Dylan-Hackett/vuulgaris-v1/docs/lpg-bergman.md

# Stereo low pass gate — Eddy Bergman's Buchla 292

Transcribed 2026-09-04 from **"RESONANT LOPASS GATE (BASED ON BUCHLA 292)",
schematic redrawn by Eddy Bergman**, 4500 x 4500 JPEG from
[eddybergman.com part 35](https://www.eddybergman.com/2020/10/synthesizer-build-part-35-resonant.html).
Raster, not vector — so unlike the BBD there is a hard resolution floor, but at
4500px the values and junctions read cleanly at 60% zoom.

## Licensing — read before this goes anywhere near a product

The drawing carries **"not for commercial use!"** in its own bottom-right corner.
`design-state.md:248` records the design as "free, he invites builds", which is
true of DIY, and §6 already notes that redrawing it is "the right move IP-wise".
Those are not the same permission. This repo also contains plans for JLC
assembly and EU sales. If this is ever sold, work from the **modularsynthesis.com
Buchla 292 source Bergman says he redrew from**, not from his drawing.

## What it is

Two vactrols per channel whose LDRs sit in the audio path, driven by a common
LED string. A 3-position mode switch reconfigures the same LDR pair as a VCA, a
2-pole resonant low pass, or both at once. `U1` is a TL084 (four sections),
`U2` a TL074 doing the CV mixing.

## Audio path, one channel

```
AUDIO IN ─┬─ R9 100K ─ GND        <- BEFORE the cap, loads the source
          └─ C6 1uF ─┬─ R10 100K ─ GND    <- AFTER it, biases the input
                     └─ U1-A pin 3 (+)
    U1-A pin 2 (−) ─┬─ R11 15K ─ pin 1 (out)
                    └─ R12 15K ─ [S1/S2] ─ GND     gain 2 with the contact made,
                                                    1 with it open
    pin 1 ─ LDR1 ─┬─ LDR2 ─┬─ R16 10K ─ [S3/S4] ─ GND
                  │        └─ U1-C pin 10 (+) ─┬─ C9 1nF ─ GND
                  │                            └─ R13 4M7 ─ GND
                  ├─ C7 220pF ─ GND
                  └─ C8 4.7nF ─ [S5/S6] ─ U1-D pin 14 (out)

    U1-C pin 9 (−) ─ R14 10K ─ pin 8 (out)         unity buffer
    pin 8 ─ R15 1K ─ AUDIO OUT
    pin 8 ─ U1-D pin 12 (+)
    U1-D pin 13 (−) ─ C10 22pF / RESONANCE 100K / R18 100K
```

**`U1-C` is the output buffer and `U1-D` is the resonance amplifier** — not the
other way round, which is the easy misreading. The LDR chain feeds `U1-C`'s
**non-inverting** input directly; `C9` 1nF and `R13` 4M7 sit on that node. `U1-C`
buffers to the output *and* drives `U1-D`, whose output returns through `C8` into
the **junction between the two LDRs** — the mid-node of the two-pole filter,
which is where resonance feedback belongs. RESONANCE sets how much comes back.

### Careful: the drawing uses "S1" for two different things

Bergman labels the **mode switch's first lug** `S1` (the red dot by `R12`) *and*
the **DEEP toggle** `S1 DEEP on/off`. They are unrelated parts. Everywhere below,
`S1`-`S6` mean mode-switch lugs only; the DEEP toggle is not fitted (see LED
drive).

### The mode switch is the whole trick

The table on the drawing is captioned **"Bottom view of toggle switch"** — it is a
**lug map, not a list of closed contacts**, and misreading it that way inverts the
whole circuit. In a 3PDT toggle the middle row of lugs is the three commons, so
**S2, S4 and S5 are commons**, and on an ON-OFF-ON the centre lever position
connects them to nothing.

| lever | contacts made | circuit |
|---|---|---|
| **VCA** | S2-S1, S4-S3 | `R12` grounded (gain 2), `R16` grounded. LDRs plus `R16` are a defined divider, response stays flat. `C8` open |
| **BOTH** (middle = OFF) | **none** | `R12`, `R16` and `C8` all open. The LDRs feed only `C7`, so the series photoresistance drops level and corner frequency **together** |
| **VCF** | S5-S6 | `C8` into the LDR1/LDR2 junction — 2-pole resonant lowpass |

**BOTH is not a combination of the other two.** It is the bare behaviour of a
photoresistor in series with a capacitor, with the switch removed from the
circuit entirely — which is the actual Buchla lowpass-gate character. VCA and VCF
are each a *modification* of it: `R16` pins the response flat, `C8` plus
resonance makes it a filter.

**Consequence for the switch part.** Poles 1 and 2 always act together, so there
are only **two** control signals — "ground `R12` and `R16`" and "connect `C8`" —
not three, and the middle position switches nothing. Stereo therefore needs
**four switched connections**, which is a quad analog switch, not the 6P3T panel
toggle this otherwise implies.

## LED drive — verified 2026-09-04 at 1.7x

`U1-B` is an **inverting** amp: pin 5 (+) runs left and straight down to `R8` 10K
to ground, **crossing `R5`'s line with no junction dot** — checked at high zoom,
and reading that crossing as a connection would turn the stage into a follower.

Its inverting input is the summing node, and OFFSET and CV arrive there
differently:

```
OFFSET pot wiper ─ R3 150K ─┬──────────── U1-B pin 6 (−)      [same node]
                            ├─ R5 100K ──────────┐
                            └─ C5 2nF ─ R4 470K ─┴─ CV in (U2-C output)
```

`C5` and `R4` are in **series with each other** and that pair is in **parallel
with `R5`** — both between the summing node and the CV node. At DC `C5` blocks,
so the CV sees 100K. Above about 170Hz it shorts and the branch becomes `R4`
470K in parallel with `R5`, i.e. 82.5K, giving the CV path roughly **1.2x more
gain at high frequency**. That is deliberate: it sharpens envelope transients to
compensate for how slow a vactrol is.

### Two feedback paths, not one

```
pin 6 ─┬─ Tp2 500K trim ──────────────────────────── pin 7 (out)   [S1 removed]
       └─ Tp1 20K trim ─ R7 33K ─┬─ LED anode node
                                 ├─ R17 100K ─ GND
                                 ├─ D1 3.9V zener, ANODE here, cathode to GND
                                 └─ VT_a LED anode
                                      VT_a cathode ─ VT_b anode
                                        VT_b cathode ─ R6 470R ─ pin 7 (out)
```

**The LED string never touches ground.** Its far end returns to the op-amp
output through `R6`; ground reaches the string only through `D1` and `R17`.

`U1-B` swings **negative**, because OFFSET sits on the positive rail and feeds
an inverting stage. So the anode node sits at **−3.9V**, where `D1` is in
reverse breakdown, and **`D1` is what supplies the LED current** — from ground,
through the string, into pin 7, which sinks it. `R6` and the output voltage set
how much. `Tp1` sets the feedback depth from that node; `Tp2` adds a second
feedback path taken straight from the output, changing overall gain.

> **Corrected 2026-09-16.** Every earlier version of this section, and the
> schematic built from it, had this backwards: `R6` on the anode side, both LED
> cathodes to ground, and `D1` reversed. That inverts the drive. With our
> op-amp swinging negative, the flipped `D1` pins the node at −0.7V and the LEDs
> never light; and where the real circuit has `D1` *supplying* LED current, the
> flipped one *shunts* it away above 3.9V. The 2026-09-11 "node by node, both
> channels, clean" check compared the netlist against this document rather than
> against Bergman's drawing, so both were wrong together — the same failure as
> U8. Fixed on the board 2026-09-16: `D301`/`D401` turned around,
> `VT302.2`/`VT402.2` moved off GND onto `LPG_LEDK_L`/`_R`, and `R306`/`R406`
> moved to sit between the LED cathodes and the op-amp output.

**Neither `S1` "DEEP" nor `Tp2` is fitted — decided 2026-09-04.** Bergman
describes DEEP as making the sound "deeper with less high tones… the effect of
turning the Offset knob counterclockwise, amount set by `Tp2`". Mechanically it
adds a second feedback path from pin 7 straight to the summing node, bypassing
the LEDs, so part of the feedback stops depending on the LED node and the LED
node has to move less to balance. Less light, gate sits more closed — an
operating-point shift, not a filter change.

With the switch permanently open that path never exists, so **`Tp2` has nothing
to do and is not fitted either.** `RT302`/`RT402` removed. `Tp1` (`RT301`/`RT401`)
stays: it is in the main loop and is still the LED-drive depth trim.

**LED reverse-voltage protection, added 2026-10.** Without DEEP's path, nothing
holds pin 7 in when the summing node goes negative (an inverted CV with CUTOFF
low), so `U1-B` saturates positive, about +10V, while the LED node sits near 0V
through `R317`. The two LEDs then take about 10V in reverse against the VTL5C3's
3.0V absolute maximum ("LED Reverse Breakdown Voltage", Xvive p1). Bergman's
circuit does the same with DEEP off. Fix:

- `D302`/`D402`, a 1N4148W in series between the LED string and `R306`/`R406`:
  anode on `LPG_LEDK_L`/`_R`, cathode on the new `LPG_LEDD_L`/`_R`, which is
  `R306.2`/`R406.2`. It carries the LED current forward and blocks the reverse
  voltage (VR 75V; 25nA max at 20V, `datasheets/1N4148W.pdf`).
- `R334`/`R434`, 2.2M across the LED pair (`LPG_LED` to `LPG_LEDK`). Two parts in
  series in reverse share the voltage by their leakage, so on its own the diode
  could leave the LEDs most of it. The resistor holds the LEDs at the diode's
  leakage times 2.2M, about 55mV at 25nA. Forward it takes about 1.4uA at 3V,
  negligible against milliamps of LED drive.

Cost: one diode drop off the ceiling of the LED drive, about 1.5mA off the 9.1mA
worst-case maximum (recheck section 06). Below the ceiling nothing changes: the
diode is inside `U1-B`'s loop, which regulates the LED anode node, so pin 7 just
sits a diode drop lower for the same LED current. `RT301`/`RT401` cannot give
the 1.5mA back; they set feedback depth, not the ceiling, which is
(Vsat - Vz - 2Vf - Vdiode) / `R306`. `R306`/`R406` stay at Bergman's 470R, so
every state is at or below his circuit's LED current. If the gate does not open
far enough on the bench, 390R there restores the ceiling (worst case 9.2mA).

## CV section — `U2` TL074

`CV1 IN` through a **Level 100K** pot, its wiper into `R28` 100K; `CV2 IN`
into `R23` 100K at `U2-A` (`R20` 100K feedback) and across the **Level + Invert
100K** pot, whose wiper feeds `R27` 100K. `R27` and `R28` both land on `U2-D`
pin 13. (Corrected 2026-09-23 — this used to say CV1 fed both, and the drop
below named `R27` as CV1's. On the drawing `R27` is CV2's and `R28` is CV1's.)
`U2-D` (12/13/14, `R30` 100K feedback) sums, `R31` 100K feeds `U2-C` (10/9/8,
`R33` 100K feedback), whose output runs back to the `R4`/`R5` summing node in the
LED driver. **`U2-B` is unused.**

## Adaptation — decided 2026-09-04

**Rails: ±12V, unchanged.** Bergman runs ±15V. Accepted as-is; the LED drive
range, the `D1` 3.9V clamp point and the `R6` 470R current all shift slightly and
the trimmers (`Tp1` depth, `Tp2` gain) absorb it. Set them on the bench.

**Three panel pots, dual-gang, one knob per stereo pair:**

| | Bergman | here |
|---|---|---|
| `RV1` **CUTOFF** | OFFSET 100K | sets the standing LED drive — how open the gate rests |
| `RV2` **RESONANCE** | RESONANCE 100K | unchanged |
| `RV3` **CV AMOUNT** | CV2 "Level + Invert" 100K | bipolar attenuverter on `LPG_ENV` |

This settles the `values.json` vs `pin-allocation.md:408-410` disagreement in
favour of `values.json`. **`pin-allocation.md` is now stale** and should be
updated to match.

**CV1 is dropped entirely** — its jack, its Level pot, and `R28`. The resistor
kept, `R328`/`R428`, is electrically Bergman's **`R27`**: CV2's attenuverter
wiper into `U2-D` pin 13. Only the designator is off by one. `LPG_ENV` from
the Daisy's CV_OUT_1 is the only control voltage.

### Dropping CV1 frees a whole op-amp package

With `R28` gone, `U2-D` has a single input, so `U2-D` + `U2-C` are two cascaded
unity inverters — a buffer. Per channel `U2` needs only **`U2-A`** (the
attenuverter's inverter) and **one summing/buffer stage**, so:

- 2 sections per channel, 4 for stereo
- **one TL074 covers both channels** instead of two
- `U2-B` was already marked "not used" on the drawing

### Mode switch

Mechanically a 3PDT ON-OFF-ON, and `SW1` here is a DPDT which cannot do it. Per
the switch reading above the circuit needs only **two control signals** and
**four switched connections** for stereo, so a quad analog switch would cover it
from one plain panel toggle — `DG419DY-T1-E3` is in `lib/vuulgaris.kicad_sym`
and commit 6724750 took that route once.

**Superseded 2026-09-11: VCA was dropped, so this is moot.** Two modes need two
switched connections, one per channel, and the DPDT does that directly. See
*VCA mode is deliberately not implemented* above.

### Vactrols — still open

Four needed, matched in on-resistance and decay across L and R. Excelitas
discontinued the line; the Xvive reissue reportedly has a brighter LED and longer
release. `design-state` §6 also carries an **unverified RoHS/cadmium** question.
No symbol or footprint in `lib/` yet.

## Checked against the drawing — 2026-09-11, both channels

> **Two rows of this table were wrong and shipped into the board: the LED drive
> and the input stage.** Both were caught by eye, 2026-09-16, by reading the
> drawing at full resolution.
>
> **Re-read in full 2026-09-23**, the 6000px image against `netmap.json` itself
> rather than against this document, cropped to full resolution wherever the
> overview was ambiguous: the pin 5/`R8` crossing (a gap, no junction), `D1`
> (anode on the LED node), pin 7's vertical (stops at the DEEP switch, never
> reaches the LED anode), the `R3`/`C5`/`R4`/`R5` node pair, the input stage,
> and the C8 → VCF → `U1-D` out return. **Every row below matches the board.**
> The one error found was a name: `R27`/`R28`, above.

`datasheets/` now holds Bergman's schematic image. `netmap.json` was diffed
against it node by node, L and R. **The two channels are structurally identical**
— every node below has the same membership on both sides, so nothing is a
one-channel typo.

Matching, and including the three things this drawing is easy to get wrong:

| node | agrees |
|---|---|
| ~~input~~ | **WRONG — `R9` sits BEFORE `C6`, `R10` after it. This row put both after the cap and the board was built that way, giving 50k of bias instead of 100k and nothing loading the source. Fixed 2026-09-16: `R310`/`R410` moved to the pre-cap node, so on our board `R310` = Bergman's `R9` and `R309` = `R10`.** |
| `U1-A` | `R11` 15K feedback |
| vactrols | LEDs in series off `R6`; LDRs in series in the audio path |
| LDR mid-node | `C7` 220pF to GND |
| **`C8` 4.7nF** | mid-node → switch → **`U1-D` output**, not to ground — the resonance injection |
| LDR2 out | `C9` 1nF and `R13` 4M7 to GND, into `U1-C` pin 10 **(+)** |
| `U1-C` | `R14` unity buffer, `R15` to output, and it drives `U1-D` pin 12 |
| `U1-D` | `C10` 22pF, RESONANCE, `R18` |
| ~~**LED drive**~~ | **WRONG — see the correction in "Two feedback paths". The string's cathode end returns through `R6` to pin 7 and `D1`'s anode is on the node. This row claimed otherwise and the board was built from it. Fixed 2026-09-16.** |
| **offset/CV sum** | `R5` 100K in parallel with the `C5`+`R4` *series* pair |
| CV chain | `U2-A` inverter, `RV3` attenuverter, `U2-D`→`U2-C` cascade |
| `U2-B` | unused, pin 5 to GND, pins 6/7 tied — as drawn |

Zero dangling nets anywhere in the block.

Deviations that are deliberate and recorded above: CV1 and `R28` dropped, `Tp2`
and the DEEP switch not fitted, ±12V rails instead of ±15V, the LED
reverse-voltage diode and its 2.2M (2026-10), and, since
2026-09-25, the **input mix** below.

### The input is a mix of the Daisy and EXT — added 2026-09-25, ADR 0011

The LPG input used to be the Daisy's output alone, into `C306`/`C406` (Bergman's
`C6`). It is now a passive two-resistor mix into that same cap:

```
AUDIO_OUT ──────┬── R301 10k ──┬── C306 1u ── U301A (+)     U301A (−) ─┬─ R311 15k ─ out
          R310 100k (R9)       │                                       └─ R312 15k ─ GND
EXT_AMP_OUT ──── R302 10k ─────┘                   (L; R channel is the 4xx set)
```

`R312`/`R412` is **Bergman's own `R12`, fitted permanently to ground** instead of
switched in for VCA mode. With it, `U1-A` runs at gain 2, which takes back the 6dB
the passive mix costs: each source reaches the LDRs at 0.95x its old level. It does
**not** implement VCA mode — that needs `R16` as well, which is still absent. Why
the mix exists, and what it costs, is in ADR 0011.

### VCA mode is deliberately not implemented — decided, do not re-raise

**This instrument ships BOTH and VCF only.** Confirmed 2026-09-11. `R16` is on
Bergman's drawing and on neither channel here, and that is the intended design,
not an omission. (`R12` was omitted too until 2026-09-25; it is now fitted
permanently for the input mix above, which is not VCA mode.)

- `R12` 15K, `U1-A` pin 2 → [S1/S2] → GND. **Now fitted as `R312`/`R412`,
  straight to ground** — `U1-A` at gain 2 on a halved input, net unity. In
  Bergman's circuit it gives gain 2 only in VCA.
- `R16` 10K, LDR2 output → [S3/S4] → GND. Omitted, so nothing pins the response
  flat — which is the whole point of VCA mode.

`SW1` compounds it. It is a DPDT using pins 1/2 and 4/5 only, so each pole is
ON-OFF rather than ON-ON, and the one thing it switches is `C8`:

| `SW1` | result | Bergman equivalent |
|---|---|---|
| closed | `C8` → `U1-D` out | **VCF** — resonant 2-pole |
| open | `C8` floating | **BOTH** — bare LDR + `C7` |

That is exactly the wanted behaviour. **BOTH is the actual Buchla lowpass-gate
character** — series photoresistance dropping level and corner frequency
together — and VCF is the resonant variant. VCA, the mode that pins the response
flat and turns the thing into a plain amplifier, is the one worth losing.

Dropping it also simplifies the hardware rather than compromising it. The
three-mode circuit needs four switched connections for stereo, which is why
*Mode switch* below reached for a `DG419DY-T1-E3` quad analog switch. Two modes
need **two** connections — one per channel — so a plain DPDT panel toggle is not
a compromise here, it is the correct part. `SW1` is already wired that way,
using pins 1/2 and 4/5 so each pole is ON-OFF.

**The DG419 proposal is therefore moot and should not be implemented.** Anyone
restoring VCA would need the quad analog switch *and* four resistors
(`R312`/`R412`, `R316`/`R416`), and that is not on the roadmap.

## Interface this has to present

| net | direction | currently |
|---|---|---|
| `AUDIO_OUT_L` / `_R` | Daisy → LPG in | via `R301`/`R401` into the input mix |
| `EXT_AMP_OUT_L` / `_R` | EXT preamp → LPG in | via `R302`/`R402` into the input mix (ADR 0011) |
| `BBD_IN_L` / `_R` | LPG out → delay | only on `R106`/`R107`, `R206`/`R207` |
| `LPG_ENV` | Daisy CV_OUT_1 → LED drive | only on `U1.C10` |
| `RV1` `RV2` `RV3` | panel, dual-gang | **placed, zero pins wired** |
| `SW1` `SW2` | panel | **placed, zero pins wired** |

## Status — in netmap and VERIFIED 2026-09-04

**748/748 connections verified, 0 unintended, 189 nets, `netcheck` exits 0.**
netmap went 169 refs / 524 connections -> **245 / 748**.

**Built exactly as the drawing shows, per channel, with CV1 removed and nothing
else reasoned away.** 14 op-amp sections, four packages:

| | |
|---|---|
| `U301` / `U401` | Bergman `U1`. A input buffer, B LED driver, C output buffer, D resonance |
| `U302` / `U402` | Bergman `U2`. A attenuverter inverter, D summer, C output inverter, **B unused with pin 5 to GND and 6 tied to 7, as drawn** |
| `VT301/302`, `VT401/402` | four VTL5C3 |
| `RT301` / `RT401` | `Tp1` 20K LED-drive depth trim, one per channel. `Tp2` not fitted |

`RV1` CUTOFF, `RV2` RESONANCE, `RV3` CV AMOUNT and `SW1` had **zero pins wired**
before this and are now connected. `SW1` pole A switches `C308`, pole B `C408` —
open is BOTH, closed is VCF.

**Removed, all by explicit decision and not by inference:** the CV1 jack, its
Level pot and `R28`; the DEEP switch and `Tp2` with it; and
`R16`, because only BOTH and VCF modes are wanted so the VCA contact is
never made. (`R12` was on this list until 2026-09-25; it is now fitted as the input
mix's gain makeup.)

### Still to do

- **F8** to pull the footprints onto the board, then place.
- The **3V9 zener** is a generic `Device:D_Zener` on a SOD-123 land — pick a real
  part before ordering.
- **Vactrol pair-to-pair spacing** in `VACTROL-TH_VTL5C3` is 12.7mm, a layout
  choice not a package dimension; the 5.08mm within each pair is from the
  datasheet and is fixed.
- **Match the four vactrols** on on-resistance and decay, L against R.
- ~~**Two knobs turn the unconventional way**~~ — **flipped 2026-09-23.** Found
  once Alpha's drawing confirmed terminal 1 is CCW: `RV1` CUTOFF had `POS12V`
  on 1/4, so clockwise *closed* the gate, and `RV3` CV AMOUNT had `LPG_ENV` on
  1/4, so clockwise was the *inverted* envelope. Bergman's drawing does not say
  which lug is CW, so neither was a departure from the source — just a choice
  nobody made. Now `RV1` is GND 1/4, `POS12V` 3/6 (**clockwise opens**) and
  `RV3` is `LPG_ENVN` 1/4, `LPG_ENV` 3/6 (**clockwise is the normal envelope,
  noon is zero**). `RV2` RESONANCE was already conventional (CW = more).
- With `R16` unfitted the LDRs work into `R13` 4M7, so at full dark the gate
  reaches about **-14dB**, not silence — the "vactrol bleed" of `design-state` §6.
