Dylan-Hackett/vuulgaris-v1/docs/pin-allocation.md

# Pin allocation

**Status: CURRENT as of 2026-08-09.** Rewritten after a cascade of changes freed six pins
and added five jacks. Safe to lay out against.

## The IO plan

**Changed 2026-08-09: the ten Daisy-facing knobs are ENCODERS, not pots.**

- **10 rotary encoders** on **2x MCP23017 I2C expanders**, both on the MAIN PCB
  beside the encoders themselves. 20 lines into the expanders, **2 wires out**.
- **3 knobs stay ANALOG POTS wired straight to the Bergman LPG board**: offset
  (dual-gang), CV amount L, CV amount R. Zero pins, zero conversion, and the
  Daisy never sees them. **Deliberate: no DAC.**
- **The MSP430 link is UART on A2/A3**, point-to-point across the cable.
  **NOT on the I2C bus.** See "why the touch link is UART" below.
- **Four jacks** (J2-J5), **corrected 2026-09-06** -- the list below used to name five
  functions for four connectors, and two of its sources have since gone internal:

  | jack | source | note |
  |---|---|---|
  | J2 CV OUT | `LPG_ENV` via `R503` 1k | **shares the LPG envelope.** Not an independent DAC -- both CV outs are spoken for |
  | J3 GATE OUT | `GATE_OUT_1` (B5) via `R504` 1k | |
  | J4 CV IN | `CV_8` (C9) | conditioned on-module |
  | J5 GATE IN / clock | `GATE_IN_1` (B10) | |

  `CV_OUT_2` (C1) is `TIME_CV` and `GATE_OUT_2` (B6) is the BBD inhibit, so neither
  reaches the panel. `CV_1`-`CV_7`, `GATE_IN_2` and `A9` are still free if a fifth jack
  is ever wanted.
- **Main encoder on U4 (GPB0-2), not the Daisy.** A9 is free (shift was dropped).
- **A8 reserved**, see below. **1-bit SD.** No panel USB.

### MSP430 reset on U4 GPB3 — added 2026-09-08

`U4.4` (GPB3) drives `MSP_RST` across `J12.3`. **This is not BSL.** Blank detection
means the Daisy never needs the entry sequence; this is a recovery reset for a
touch chip that has hung, and the way to re-arm the BSL after SLAU550 §3.4's
ten-second time-out without power-cycling the module.

**On an expander GPIO, not a Daisy pin**, for three reasons. Every Daisy candidate
is gone — `B5` is the gate out jack, `B6` the BBD inhibit, `A9` the OLED reset,
`A8` reserved. U4 had GPIO to spare (it is full now, see "GPA7 and GPB7" below). And the expander runs on `P3V3_DAISY` against an
MSP430 absolute max of 3.6V, so it is a **direct wire with no divider** — which
is precisely what [Q13](notes/open-questions.md) called a day lost with a logic
analyser. Being on I2C rather than the UART also means it still works when the
touch chip is too wedged to answer on the serial link.

> **This makes a faceplate part load-bearing.** MCP23017 GPIO power up as
> **inputs (high-Z)**, so `MSP_RST` floats until firmware configures GPB3. The
> pullup and capacitor TI specifies on RST/NMI must be on the faceplate. It was
> good practice before; it is now required.

`MSP_TEST` stays undriven on `J12.1`. **No external pulldown** (corrected 2026-09-28; this
said it "still wants a pulldown at the chip end"): SLASEO5D Table 7-4 says an unused TEST is
left "Open. This pin always has an internal pulldown enabled", and Figure 10-4, TI's
Spy-Bi-Wire connection, puts nothing on it.

(J12 pin numbers changed 2026-09-25, when `J12` moved to the back of the main board facing
down — see `hardware/faceplate/README.md` §5 for the full pin map.)

### Four channel buttons — added 2026-08-16

**Four momentary buttons on U4's spare GPIO**, one per channel, sitting in the left
margin beside the pads. They cost **no Daisy pins**: U3 is full at 16 GPIO for eight
encoders, but U4 only used 4 of 16 for ENC9/ENC10, so the buttons take `GPA4`-`GPA7`
and eight of its GPIO are still free after them.

| Button | Net | U4 pin |
|---|---|---|
| SW4 | `BTN1` | 25 (GPA4) |
| SW5 | `BTN2` | 26 (GPA5) |
| SW6 | `BTN3` | 27 (GPA6) |
| SW7 | `BTN4` | 7 (GPB6), was 28 (GPA7) until 2026-10 |

Wired **button to ground with the MCP23017's internal pull-ups enabled** — the same
arrangement as the encoders, so no external resistors. Polled with everything else at
500Hz, i.e. 2ms, which is irrelevant for a button.

**Placement, revised 2026-08-17:** the controls sit in the left margin centred on panel
**x 33.571** — the main encoder at y 76.525, then the four keys as a **2x2 Cherry MX
cluster** on 19.05mm pitch at x 24.046 / 43.096, y 100.725 / 119.775. The pad block moved
**20mm right** to open that margin, so the pads now run x 61.143-277.143. The encoder
used to sit in the RIGHT margin; it moved with the keys so the UI reads as one group.

**There is no shift button.** It was dropped 2026-08-16 — the four keys are general UI
keys, not per-channel modifiers, which is why they read better as a cluster than a
column. A9 came back with it.

Everything else on the panel is unchanged — the ten parameter encoders, three pots, two
DPDT switches and the OLED keep their coordinates, because the upper region is centred
independently of the pad block.

**This displaced the MSP430 power cluster**, which was in that left margin. It moved to
pcb (40-62, 98-105) — still nowhere near the OLED rail, which is the only thing §5.5
actually requires of it.

**`placement-panel-facing.txt` is now genuinely generated:**
`python3 mockups/generate-faceplate.py --placement > hardware/placement-panel-facing.txt`.
It previously claimed to be generated while being hand-maintained, which let the panel
artwork and the PCB placement drift apart with nothing to catch it.

**Net names are placeholders.** `BTN1`-`BTN4` should be renamed once the function is
decided (mute? solo? channel select? record-arm?).

### Two links, deliberately separate

| Link | Daisy pins | Devices | Crosses the cable? |
|---|---|---|---|
| **UART4** | **A2** (RX), **A3** (TX) | MSP430FR2675 | **yes**, point-to-point |
| **I2C1** | B7 (SCL), B8 (SDA) | MCP23017 x2 @ 0x20, 0x21 | **no**, main PCB only |

### Poll rates, and the arithmetic behind them

Quadrature edges per second is `rev/sec x PPR x 4`. For a 24-PPR encoder that is
**96 edges per revolution**, so:

| turn | rev/sec | edges/sec | at 500Hz | at 2kHz |
|---|---|---|---|---|
| deliberate parameter twist | ~1 | ~96 | 5 samples/edge | 21 |
| **fast menu flick** | 3-5 | **288-480** | **1-2 samples/edge** | 4-7 |

**ENC1-ENC10 stay at 500Hz** — about 24% of a 400kHz bus for both expanders. Parameter
knobs are turned deliberately and never flicked through a list.

**U4's Port B is polled at 2kHz** because ENC0 lives there and ENC0 is the one encoder
that does get spun hard. One GPIOB read is about 100us, so that is roughly 20% more bus.

### GPA7 and GPB7 are output only, moved 2026-10

Microchip's MCP23017 datasheet, since Revision D (June 2022) and still in
Revision E (DS20001952E, July 2026), says "Pins GPA7, GPB7 are output only for
MCP23017" (Features, and Table 2-1). The reason Microchip gave publicly: a
transition on either pin while it is an input can corrupt SDA, i.e. the whole
bus both expanders share. The silicon did not change; every part has it. The
copy in `datasheets/` is Revision C, which predates the note, and this board
had `ENC4_B` on U3 GPA7, `ENC8_B` on U3 GPB7 and `BTN4` on U4 GPA7.

| net | was | now |
|---|---|---|
| `ENC4_A` | U3.27 GPA6 | U4.23 GPA2 |
| `ENC4_B` | U3.28 GPA7 | U4.24 GPA3 |
| `ENC8_A` | U3.7 GPB6 | U4.5 GPB4 |
| `ENC8_B` | U3.8 GPB7 | U4.6 GPB5 |
| `BTN4` | U4.28 GPA7 | U4.7 GPB6 |

Both lines of each encoder moved, so a quadrature pair is still read from one
port in one I2C transaction. All four GPA7/GPB7 pins (U3.8, U3.28, U4.8, U4.28)
are tied to `GND`: every pin is an input from power-up until firmware writes
IODIR, and a grounded pin cannot transition in that window. **Firmware sets
them as outputs driven low and never drives them high.** ENC8 and BTN4 now share
U4 port B with ENC0, so they get its 2kHz poll; ENC4 on port A is read at 500Hz
like the other parameter encoders. U3 GPA6 and GPB6 are now free; U4 has none.
Plan and sources: `docs/review/recheck/fix-mcp23017-gpa7-gpb7.md`.

*An earlier revision of this document claimed hands produce "20-30 transitions per
second". That is about 0.25 rev/sec — too slow even for a deliberate twist, and it is
what made 500Hz look sufficient everywhere. The table above supersedes it.*

**The encoders are DETENTLESS** (decided 2026-08-13, see the brief §4.1). The original
C202365 was an EC11E18244AU at 36 detents/18 pulses and is withdrawn — thirty-six
clicks per turn is wrong for ten continuously-variable parameters. The replacement part
is not yet chosen; it gates on stock, on shaft length (which waits on enclosure
height), and on ENC0 needing a push switch the other ten do not.

### Why the touch link is UART, not I2C

**TI's CapTIvate protocol is 2 wires over UART and 3 over I2C.** From the
CapTIvate Technology Guide: *"the UART operates in a full duplex mode using RX
and TX pins, and the I2C operates as an I2C Slave using SDA and SCL pins with an
additional pin P1.2/IRQ to generate interrupt requests."*

**That third wire would be A8**, the pin reserved for the BBD clock. I2C for the
touch chip costs the delay upgrade.

Four more reasons, on this board specifically:

| | |
|---|---|
| **Point-to-point** | a hung touch chip cannot take the encoders down with it |
| **Push-pull, not open-drain** | actively driven both ways, across a cable |
| **Self-resynchronising** | a glitch costs one frame. I2C can leave a slave stuck mid-byte holding SDA low, recoverable only by a deliberate routine |
| **Low impedance both states** | I2C idles high through a pull-up, and high-impedance nodes couple more into a capacitive front end |

**I2C's one real advantage was that the master supplies the clock**, so there is
no baud agreement and no exposure to oscillator drift. **That is retired by the
32.768kHz crystal** on pins 46/47, which cost about $0.20 and were already free.

Both interfaces are officially supported by CapTIvate, so this is not off-label
either way.

### Why encoders freed ten analog pins

The ten pots were the entire ADC budget. Moving them to expanders returns:

| Freed | Kind |
|---|---|
| **CV_1 to CV_7** | **conditioned, rated to the +/-12V rails** |
| D8 | bare 0-3.3V ADC |
| ~~A2, A3~~ | *spent again on the touch UART* |

**CV_8 already carries the CV in jack, so this makes eight conditioned CV
inputs available** on an instrument that had one. That is a larger change to
what the product *is* than the encoders themselves.

### What this costs

| | |
|---|---|
| 10x detentless encoder (part TBD; C202365 withdrawn) | +$12.12 **[stale — detentless parts cost more]** |
| less 10 pots no longer needed | -$7.00 |
| 2x MCP23017 | +$3.60 |
| **Net** | **+$8.72, about 5% of BOM** |

**The panel stops being readable at a glance.** No knob position to see. On a
Salamis counting board, whose visual logic is positions on lines, that is a
real loss and it was accepted knowingly.

**The three analog pots are the exception, and that reads as intentional.**
Pots with end stops for the analog domain, endless encoders for the digital
one. The offset knob is already drawn larger than the rest, so the distinction
is visible before it is felt.

**Consequence, accepted:** offset and CV amount L/R cannot be saved in a preset
or shown on the OLED, because nothing digital is in their path. Load a patch
and those three are wherever they were physically left.

---

## The full header

| Pin | Use | | Pin | Use |
|---|---|---|---|---|
| A1 | -12V in | | B10 | **GATE IN / clock** |
| **A2** | **MSP430 UART RX** | | C1 | **CV OUT jack** |
| **A3** | **MSP430 UART TX** | | **C2-C8** | **free** (CV_1-CV_7, conditioned) |
| A4 | GND | | **C9** | **CV IN jack** (CV_8) |
| A5 | +12V in | | C10 | LPG envelope (one, splits analog) |
| A6 | 5V out | | D1 | OLED CS |
| A7 | GND | | D2 | OLED DC |
| **A8** | **RESERVED** | | **D3, D4** | **FREE** (SDMMC_D2, SDMMC_D1) |
| A9 | **OLED RES** (was listed FREE until 2026-09-21) | | D5, D6, D7 | SD 1-bit: D0, CLK, CMD |
| A10 | 3V3 out | | **D8** | **free** (ADC) |
| B1-B4 | audio out/in L/R | | D9 | OLED MOSI (native SPI2) |
| B5, B6 | **GATE OUT 1, 2** | | D10 | OLED SCK |
| B7, B8 | **I2C** (2 expanders, local) | | | |
| **B9** | **FREE** (GATE_IN_2) | | | |

**Bidirectional GPIO 15 of 16. ADC 8 of 12 free** (CV_1-CV_7 and D8). A2 and A3
are now the touch UART, CV_8 is the CV in jack, D9 is SPI MOSI.

### The CV pins are NOT in ascending order

**Verified 2026-08-12 against the Patch SM symbol.** "C2-C8 = CV_1-CV_7" above is
shorthand for *which pins are free*, *not* a 1:1 map. The first four are reversed:

| Pin | C2 | C3 | C4 | C5 | C6 | C7 | C8 | C9 |
|---|---|---|---|---|---|---|---|---|
| **Signal** | CV**4** | CV**3** | CV**2** | CV**1** | CV5 | CV6 | CV7 | CV8 |

Wire a jack to C2 expecting CV_1 and you get CV_4. This costs nothing if the jacks
are labelled from this table and a silkscreen respin if they are not.

---

## A8 is reserved for a delay in a later revision

**Decision 2026-08-09: build V1 without the analog delay, but do not spend A8.**

The delay work (see [workflow.md](workflow.md) and the BBD investigation) concluded that a
BBD's **two-phase clock can be generated from a 74HC74 divide-by-two fed by a single Daisy
timer pin**, which makes delay time a firmware parameter locked to the loop clock. That
needs exactly one pin, and **A8 is PB14, which has a hardware timer on it.**

Spending A8 on anything else closes that door. Nothing else currently needs it.

### What else to reserve now, while it is free

| Reserve | Cost now | Why |
|---|---|---|
| **A8** | 0 | the BBD clock, from a hardware timer |
| **0R links in the audio path** where a delay would insert | pennies | a later daughterboard taps in without cutting traces |
| **Board area** beside the LPG section | 0 | ~30 x 40mm is enough for a stereo BBD |
| **2-3 spare pins on the inter-board connector** | 0 | connector pins are free, Daisy pins are not |

### Explicitly NOT fitting: a DAC

An MCP4728 quad DAC on the I2C bus would make offset and CV amount L/R
presettable and OLED-visible. **Decided against 2026-08-09.** Those three
controls go straight to the Bergman board as analog pots, and that is the whole
point of them. Address 0x60 is left unused on the bus if that ever changes.

---

## The USB decision

**Patch SM has two independent USB ports**, verified against the Rev3 schematic
(`ES_Daisy_Patch_SM_Schematic.pdf`) and libDaisy source. This was originally documented wrong
and it cost two usable pins.

| Port | Peripheral | Pins | On the header? | libDaisy role |
|---|---|---|---|---|
| **Onboard Micro USB** | USB_OTG_FS | PA11 / PA12 (+PA9 VBUS) | **No.** On the module itself. | `usbd` = **device**: DFU flashing, USB MIDI |
| **A8 / A9** | USB_OTG_HS | PB14 / PB15 | Yes | `usbh` = **host**: USB drives, future USB MIDI host |

**DFU flashing and USB MIDI never touch A8/A9.** They run on the module's own connector. The
schematic notes it "allows for powering of the MCU from just USB (allowing for pre-flashing,
etc. without having to have it powered by eurorack)."

**Decision: spend A8/A9 on IO.**

| Given up | Kept |
|---|---|
| Panel-mounted USB jack | **DFU** over the module's onboard Micro USB |
| Bootloader firmware-from-USB-drive | **SD card firmware drop** |
| Future USB MIDI host (plug in a keyboard) | **USB MIDI device**, when the module is reachable |

**Revised 2026-08-17: the module's connector is now exposed, so there is no practical cost.**
U1 sits rotated 90 degrees hard against the right wall, putting its USB-C at pcb (282.5, 85.2),
1.8mm inside the edge. Cut the enclosure for it there. This costs no pins — DFU and USB MIDI
device both run on that connector, and A8/A9 stay free for IO exactly as decided above.

The layout constraint that produced this: **USB, the D header and the C header are all on the
same long edge of the module**, so whichever wall the USB faces, the SD and CV face it too.
Only the right wall works — the left is blocked by ENC0 and the MX cluster (about 16mm clear
against the module's 68mm), and the top 47mm is entirely panel controls.

**The SD card is not user-accessible, and that is accepted.** The module occupies 68mm of the
77mm of clear height at that wall, so J1 cannot sit beside its own D header; it is parked to
the left at (234, 114), a 44mm run, with the module between. Swapping a card means opening the
case. Fine, because firmware ships over USB now and samples are written over the wire.

**Build the bootloader with the default config**, i.e. **without** `DSY_DFU_USE_EXT_USB`. That
flag moves DFU to the external port, which no longer exists on this board.

---

## Daisy Patch SM

### Bidirectional GPIO: 15 of 16 used, A8 reserved

| Function | Pins | Note |
|---|---|---|
| **I2C** | **B7** SCL, **B8** SDA | **2x MCP23017 only, both local.** Pull-ups once, on the main PCB. |
| **MSP430 UART4** | **A2** RX, **A3** TX | point-to-point across the cable |
| SD 1-bit | **D5** (D0), **D6** (CLK), **D7** (CMD) | Fixed SDMMC1 pins |
| OLED SPI2 | **D1** (CS), **D9** (MOSI), **D10** (SCK) | D9 is the **native** SPI2_MOSI |
| OLED DC | **D2** | Any GPIO |
| Main encoder A, B | **D3**, **D4** | The one beside the pads. The other ten are on expanders. |
| Shift button | **A9** | Internal pull-up, button to ground, `daisy::Switch` |
| **A8** | **RESERVED** | BBD clock in a later rev. Do not spend. |
| **D8** | **FREE** | ADC-capable, bare 0-3.3V |

### The main encoder moved to U4 — and poll Port B at 2kHz

**Revised 2026-08-19.** ENC0's A, B and push now go to **U4 GPB0, GPB1, GPB2**
instead of D3, D4 and B9. U4's Port B was completely unused; U3 is full at 16/16.

It was on the Daisy for latency. The reason it can move is that the real problem
was never latency, it was the **500Hz poll rate**:

```
realistic fast flick   3-5 rev/sec on a 24-detent encoder
                       = 72-120 detents/s = 288-480 quadrature transitions/s

 500 Hz  ->  1-2 samples per transition   marginal, drops steps
2 kHz    ->  4-7 samples per transition   comfortable
```

**So poll GPB on U4 at 2kHz.** One GPIOB read at 400kHz is about 100us, so 2kHz
costs ~20% of the bus. The ten parameter encoders can stay at 500Hz — knobs do not
get flicked through a menu.

**An interrupt line was considered and rejected.** U4's INTB (pin 19) is free and
could drive a freed Daisy pin, but the MCP23017's INT latches until GPIO or INTCAP
is read, and any code path that misses that clear leaves the encoder dead
intermittently. It also does not make the decode lossless -- the part queues
nothing, so a fast spin can still slip a transition between the interrupt and the
I2C read. Fixed-rate sampling is what a quadrature decoder wants anyway.

**What this bought:** about 508mm of trace (ENC0 sat 250mm from the Daisy's D
header and 75mm from U4), and **D3 and D4 back, both SDMMC data lines** -- 4-bit SD
now needs only D2, currently OLED DC.

### Two pins came back, and it is worth recording why

**The MSP430 IRQ line was redundant.** It existed so the Daisy would know when to poll, which
is an I2C requirement. **Over UART the MSP430 simply transmits and the Daisy's RX interrupt
fires by itself.** Dropping the wire freed **A8**. Keep the footprint in case of an I2C
fallback, but do not allocate the pin.

**BSL does not need RST and TEST from the Daisy.** SLAU550 section 3.3.1: the BSL can be
invoked by application software, by calling the Z-area at 0x1000. So the Daisy sends an
"enter BSL" command over the existing UART and reflashes over the same two wires.
**That freed B5 and B6 to be real 0-5V gate outputs.** The SBW pads stay on the board as the
recovery path for a touch chip too broken to receive the command.

**Confirmed 2026-09-06 for the blank-chip case too, which this paragraph did not cover.**
Software invocation needs firmware already on the chip to make the call, so it says nothing
about the first flash of a part fresh off the reel. SLAU550 Rev AB §3.3.3 closes that: the
FR26xx boot code does **blank device detection** and jumps straight into the BSL when the
reset vector reads 0xFFFF, which *"eliminates the need for two additional wires (TEST, RST)"*.
A blank FR2675 answers over the UART unaided. `R26`-`R29` are deleted and `GATE_OUT_2` now
drives the BBD inhibit. Watch the **ten-second BSL time-out** instead —
[ADR 0005](decisions/0005-bsl-over-daisy-uart.md).

**And CV amount moving to analog freed D8 and D9.** MOSI returned to its native D9, which in
turn freed **A9** for the shift button.

### OLED + microSD + Patch SM together — checked 2026-09-11

They coexist because they sit on **different peripherals**, not on a shared bus:

| function | Patch SM pin | STM32 | peripheral |
|---|---|---|---|
| `OLED_CS` | D1 | PB4 | SPI2_CS |
| `OLED_MOSI` | D9 | PC3 | SPI2_MOSI (alt; D9's primary is ADC_11) |
| `OLED_SCK` | D10 | PD3 | SPI2_SCK |
| `SD_D0` | D5 | PC8 | SDMMC1_D0 |
| `SD_CLK` | D6 | PC12 | SDMMC1_CLK |
| `SD_CMD` | D7 | PD2 | SDMMC1_CMD |

No pin is shared. SPI2 and SDMMC1 are independent blocks, so the display and
card can be driven at the same time without arbitration.

**Two pins are borrowed as plain GPIO, and one of them has a consequence:**

- **`OLED_DC` on D2, which is `SDMMC1_D3`.** This is what **locks the SD to
  1-bit mode**, permanently. 4-bit needs D2, D3 and D4 together; D3 and D4 are
  free but D2 is not, so freeing 4-bit means moving `OLED_DC` — and the only
  remaining free GPIO in the bank is **D8** (`ADC_12`/PC2). Worth knowing before
  anyone assumes D3/D4 being free is enough.

  1-bit SDMMC1 at 50MHz is ~6 MB/s against ~25 MB/s for 4-bit. Ample for sample
  playback; it is a ceiling, not a problem.

- **`OLED_RES` on A9, which is `USB_DP`.** Legal — the datasheet lists A8/A9 as
  GPIO — but it forecloses ever using the broken-out USB pins as USB. A8
  (`USB_DM`) is still free and useless on its own. MIDI was dropped and firmware
  loads over the module's own micro-USB, so nothing is lost today; the door is
  simply shut.

#### Demonstrated in libDaisy, not just non-conflicting on paper

Pin assignments that do not collide are not the same as a combination known to
work. The evidence is in the vendor library, in the tree at `fw-daisy/libDaisy`:

`src/per/sdmmc.cpp` guards the three extra data pins behind the width check, so
in 1-bit mode the SD driver never claims PC11:

```c
GPIO_InitStruct.Pin = GPIO_PIN_12 | GPIO_PIN_8;
if(sdHandle->Init.BusWide == SDMMC_BUS_WIDE_4B)
    GPIO_InitStruct.Pin |= GPIO_PIN_9 | GPIO_PIN_10 | GPIO_PIN_11;
```

`src/dev/oled_ssd130x.h` then defaults its soft-SPI transport to **the same pins
this board uses**:

```c
pin_config.sclk = Pin(PORTD, 3);   /**< D10 - SPI2 SCK  */
pin_config.mosi = Pin(PORTC, 3);   /**< D9  - SPI2 MOSI */
pin_config.dc   = Pin(PORTC, 11);  //D2
```

`DC` defaulting to D2 — which *is* `SDMMC1_D3` — is the vendor themselves
assuming a 1-bit card alongside the display. The hardware-SPI transport
separately defaults `reset` to `Pin(PORTB, 15)`, which is A9. Every borrowed pin
on this board is a pin libDaisy borrows the same way.

**FIRMWARE FOOTGUN — the library default breaks this board.**
`SdmmcHandler::Config::Defaults()` sets `width = BusWidth::BITS_4`. Calling
`Defaults()` and not overriding it will reconfigure PC11 to SDMMC alternate
function and kill the display's D/C line — a dead OLED with no hardware fault to
find. Firmware must carry:

```c
SdmmcHandler::Config sd_cfg;
sd_cfg.Defaults();
sd_cfg.width = SdmmcHandler::BusWidth::BITS_1;   // REQUIRED: D2 is OLED_DC
```

**One gap to close in firmware:** the soft-SPI transport has no CS pin at all —
only sclk, mosi, dc, reset. This board wires `OLED_CS` to D1, so firmware must
drive D1 low itself, or use the hardware-SPI transport reconfigured from its
SPI_1/PORTG defaults onto SPI2.

**The SD wiring is textbook 1-bit SDIO.** `SD_CMD` and `SD_D0` carry 47k pullups
to `P3V3_DAISY` (`R506`, `R507`); `SD_DAT3` carries a 47k pullup (`R508`) and is
deliberately **not** routed to the Daisy, which is what holds the card out of SPI
mode. `SD_CLK` has no pullup, correctly. DAT1/DAT2 are left unconnected.

**The OLED's font ROM is deselected, not forgotten.** `OLED_FONTCS` (DS1.9) is
pulled high through `R505` 10k, and DS1 pin 8 — the font ROM's MISO — is
unconnected to match. The Daisy renders its own glyphs.

**Rails:** the OLED runs on its own 3V3 (`U5` AMS1117 fed from the Daisy's 5V
through ferrite `FB1`), separate from `P3V3_DAISY`. Both originate at the
module, so `P3V3_OLED` comes up an LDO's worth *after* `P3V3_DAISY` and the
Daisy can briefly drive display pins into an unpowered rail at boot. Short,
same-source and normally harmless — but firmware should hold `OLED_RES` low
until the rail is up rather than relying on that.

### Input-only and output-only pins

| Function | Pin | Note |
|---|---|---|
| **CV_1 to CV_7** (C2-C8) | **FREE** | Input only, conditioned. Seven more CV jacks available. |
| **CV IN jack** | **CV_8** (C9) | **Conditioned on-module. Rated to the +/-12V rails.** |
| **GATE OUT 1** | **B5** (GATE_OUT_1, PC14) | Native 0-5V, no buffer needed |
| **GATE OUT 2** | **B6** (GATE_OUT_2, PC13) | Same |
| **GATE IN 2** | **B9** (GATE_IN_2, PG14) | **Free.** Was the main encoder push before it moved to U4. |
| **GATE IN / clock** | **B10** (GATE_IN_1, PG13) | Doubles as the external envelope trigger |
| LPG envelope out | **CV_OUT_1** (C10) | **One output.** Splits on the LPG board into the two analog CV-amount attenuators. |
| **CV OUT jack** | **CV_OUT_2** (C1) | Freed because one envelope needs one DAC |

### Not a GPIO

| Function | How |
|---|---|
| OLED RST | **RC / pullup, no GPIO.** |
| LPG offset, CV amt L, CV amt R | **Analog, on the LPG board.** |
| Mode switch, source switch | **Analog DPDT routing on the LPG board.** |

---

## Why the CV in moved off D8, and onto CV_8

**Corrected 2026-08-09.** The CV jack was briefly on D8, which would have needed a divider,
an offset and clamp diodes, and would have destroyed the pin without them. **Swapping it with
a channel pot removes the entire problem**, because the module already conditions CV_1-CV_8.

Straight from the Patch SM absolute maximum ratings:

| Pin type | Min | Max |
|---|---|---|
| **CV input** | **negative power in** | **positive power in** |
| GPIO | -0.3 V | 6 V |

**A CV input is rated to the power rails**, so at +/-12V it survives anything a modular can
patch into it, with 100K input impedance and the conditioning already on the module. **A GPIO
dies above 6V.**

And the swap is free in the other direction: **a pot is a benign 0-3.3V source**, so it is
perfectly happy on a bare ADC pin. Wire it to **3V3 (A10)**, not 5V.

| | Was | Now |
|---|---|---|
| CV jack | D8, bare 0-3.3V pin | **CV_8 (C9)**, conditioned, +/-12V tolerant |
| 8th channel pot | CV_8 | gone: it is an encoder now, D8 is free |
| External parts needed | divider + offset + 2 clamp diodes | **none** |

**The lesson worth keeping:** put the hostile signal on the pin that was built to survive it,
and the benign one on the pin that was not.

---

## Analog headroom: ten pins, and seven of them conditioned

Moving the knobs to encoders inverted this section. It used to read "all 12 ADC
pins are allocated, there is no headroom".

| Free | Kind | Good for |
|---|---|---|
| **CV_1 to CV_7** (C2-C8) | conditioned, rated to the rails | **CV input jacks** |
| D8 | bare 0-3.3V | a pot, a trimmer, anything benign |

Only **CV_8** (the CV in jack) and **ADC_11 / D9** (spent on SPI MOSI) are taken.

**Do not put a CV jack on D8.** Those are bare GPIO rated -0.3 to 6V.
See "Why the CV in moved off D8" above; the reasoning did not change just
because there are now spare pins.

## Pot wiring: only three pots remain

| Pot | Goes to | Note |
|---|---|---|
| LPG offset (dual-gang) | Bergman board | never seen by the Daisy |
| CV amount L | Bergman board | attenuates CV_OUT_1 |
| CV amount R | Bergman board | attenuates CV_OUT_1 |

The 5V-vs-3V3 reference trap that used to live here is **gone with the pots**.
Nothing analog reaches the Daisy any more except the CV in jack on CV_8, which
is conditioned on-module.

### Envelope and LPG control map

**One envelope, one DAC output.** The split into left and right happens in analog.

```
        [ one envelope, in firmware ]
                     |
              CV_OUT_1 (C10)          <- ONE output. CV_OUT_2 is now a jack.
                     |
        +------------+------------+
        |                         |
   x CV amt L                x CV amt R     <- ANALOG pots on the LPG board
        |                         |
        v                         v
   [ L LPG ]  <----  +  ---->  [ R LPG ]
        ^                         ^
        +-------- offset ---------+
              (dual-gang analog pot)
```

Each LPG control input is **analog offset + (envelope x CV amount)**.

**Attenuating after the DAC rather than in firmware is the better engineering**, not just the
cheaper wiring: the CV outputs are 12-bit, so scaling to 10% in software would leave you using
about 400 of 4096 codes. Attenuating in analog keeps the DAC at full scale at every setting.

**The mode switch is ONE switch, not one per channel.** The LPG is a single **stereo** unit, so
VCF-or-VCA is one decision applied to both sides at once: a **DPDT toggle, one pole per stereo
side, ganged on a single actuator**. The panel's second slot is the unrelated **source** switch
(resample or external input), also DPDT for the same L/R reason.

**Consequence of offset and CV amount being analog:** they cannot be stored in a preset or
shown on the OLED. **The quad DAC above fixes this**, and is the reason to fit it in V1.

**The envelope now has an external trigger: B10.** That was the open architectural question.
It can still fire internally from touch onset, note events or the sequencer, but the jack
exists.

---

## MSP430FR2675 (PT / LQFP-48)

**Verified against the datasheet**, SLASEO5D revised September 2021. Pin numbers are the PT
column of Table 7-2.

### CapTIvate electrodes: all 16 used

4 pads x 4 electrodes. This consumes the entire self-cap capacity, and it constrains
everything else.

**Corrected 2026-09-28: each pad takes ONE PIN FROM EACH BLOCK, not one block.** Pads are
numbered 1-4 from the jack edge. Element `E0n` is block `CAPn`, so `RXn` of pad `p` goes to
`CAPn.(p-1)`:

| Pad | RX0 -> E00 | RX1 -> E01 | RX2 -> E02 | RX3 -> E03 |
|---|---|---|---|---|
| 1 | CAP0.0 (23) | CAP1.0 (27) | CAP2.0 (32) | CAP3.0 (36) |
| 2 | CAP0.1 (24) | CAP1.1 (28) | CAP2.1 (33) | CAP3.1 (37) |
| 3 | CAP0.2 (25) | CAP1.2 (29) | CAP2.2 (34) | CAP3.2 (38) |
| 4 | CAP0.3 (26) | CAP1.3 (30) | CAP2.3 (35) | CAP3.3 (39) |

A block measures **one pin at a time**: SLASEO5D §9.10.14, "4 CapTIvate measurement blocks to
enable parallel scanning of up to 4 electrodes simultaneously (**one electrode per block**)".
The CapTIvate Technology Guide's 4-element slider figure (Design Guide, "Sliders and Wheels")
labels the blocks themselves E00-E03 and says "Select one pin from each CAP IO block"; the
same pin number in every block puts all four elements in one measurement cycle. So each pad
is one cycle with all four elements in parallel, and the four pads are four cycles.

This table used to put each pad's four electrodes in **one block** (pad 1 = CAP0.0-0.3, and
so on). That measures a pad's elements in four separate cycles with the idle ones held at
ground -- the linearity loss [ADR 0002](decisions/0002-msp430fr2675-for-touch.md) chose a
four-block part to avoid. The cost of the fix is fan-out: a pad's four lines leave the
package from four places instead of four neighbouring pins.

### Serial link: eUSCI_A and eUSCI_B do NOT share pins

**Q2 is resolved. No 0R jumpers needed.** Route both UART and I2C; select in software.

| Interface | Module + mapping | PT pins | Verdict |
|---|---|---|---|
| **UART** | UCA0 default (P1.4 TXD / P1.5 RXD) | **4 / 5** | **Use this.** Runtime and BSL become the same two wires — see "Inter-board interface". Pin 4 also carries VREF+ and TCK, both idle here. |
| UART | UCA0 remapped (P5.2 TXD / P5.1 RXD) | 45 / 44 | **Not used.** No conflicts, but runtime and BSL would stop being the same wires. Was a fallback until Q21 closed (2026-09-27). |
| UART | UCA1 (P2.6 TXD / P2.5 RXD) | 30 / 29 | **Unusable. Collides with CAP1.3 and CAP1.2.** |
| **I2C** | UCB0 default (P1.2 SDA / P1.3 SCL) | **14 / 15** | **Use this.** No conflicts. |
| I2C | UCB0 remapped (P4.6 SDA / P4.5 SCL) | 18 / 17 | Also fine. |
| I2C | UCB1 default (P3.2 SDA / P3.6 SCL) | 38 / 39 | **Unusable. Collides with CAP3.2 and CAP3.3.** |
| I2C | UCB1 remapped (P4.4 SDA / P4.3 SCL) | 9 / 8 | Fine. |

**The two traps are UCA1 UART and default UCB1 I2C.** Both land on CapTIvate electrode pins.
With all 16 electrodes in use they are simply not available, and picking one by habit gives a
board that cannot talk and cannot sense.

Mapping is selected by the **`USCIA0RMP` / `USCIBxRMP` bits** in `SYSCFG2` / `SYSCFG3`.
Datasheet footnotes 3 and 4: **only one selected port is valid at any time.**

### System pins

| Function | PT pin |
|---|---|
| DVCC | 1 |
| DVSS | 48 |
| **RST / NMI / SBWTDIO** | **2** |
| **TEST / SBWTCK** | **3** |
| VREG (CapTIvate regulator decoupling cap) | 31 |
| VREF+ | 4 |

**VREG on pin 31 needs an external decoupling cap.** It is the CapTIvate regulator output, not
a supply input. Easy to miss.

---

## Inter-board interface

| Signal | Faceplate side | Main board side |
|---|---|---|
| 3V3 | DVCC (pin 1) | **Its own LDO.** Not shared with the OLED or audio. |
| **GND x2-3** | DVSS (pin 48) | More than one. Cheapest noise mitigation there is. |
| **UART TXD** | **pin 4 (P1.4), DEFAULT UCA0** | **A2** (UART4_RX) |
| **UART RXD** | **pin 5 (P1.5), DEFAULT UCA0** | **A3** (UART4_TX) |
| IRQ | footprint only | **Do NOT wire to A8.** Redundant over UART. |
| **BSL RST** | pin 2 | **Test pad only.** Software BSL invocation instead. |
| **BSL TEST** | pin 3 | **Test pad only.** |

**Use the DEFAULT UCA0 mapping, pins 4 and 5.** [Q21](notes/open-questions.md) is
**closed (2026-09-27)**: SLASEO5D Table 9-4 puts the UART BSL on P1.4 (transmit) and
P1.5 (receive), so runtime UART and BSL UART are the same two wires. Pin 4 also
carries TCK and VREF+, but **SBW is 2-wire so TCK is idle**, and CapTIvate does not
use VREF+. **47k pull-ups on both lines** at the MSP430 (SLAU550 §3.3.2.1: floating
TCK/TMS invite JTAG mode).

**The remapped 44/45 fallback is dropped.** It only covered the BSL being on other
pins, and `J12` as built has no free position for it: five signals and five grounds,
the grounds because this cable carries digital edges into a capacitive sensing front end.

**No I2C crosses this cable any more.** The expanders are local to the main PCB.

**SBW test pads** (TEST pin 3, RST pin 2, 3V3, GND) are now the *only* hardware BSL path, and
they are the recovery route for a touch chip whose firmware is too broken to accept the
software invocation. Put them on the board: free, and the difference between a repair and a
scrapped faceplate.

**Test points on all four signals** (UART Tx, Rx, RST, TEST). When BSL does not work first
time, you want a scope probe point that is not an LQFP pin.

**Regulate 3V3 on the main board and filter locally at the MSP430.** Do not share a rail with
audio circuitry. The LPG runs on +/-12V, so there is a regulator in the chain already.
