Dylan-Hackett/vuulgaris-v1/docs/notes/open-questions.md

# Open questions

Every `[unverified]` flag and unresolved conflict from `../design-state.md`, ordered by what
it blocks. **Nothing open here should drive a decision until it is closed.**

**Resolved: Q2, Q3, Q4, Q5, Q6, Q8, Q9, Q11, Q12, Q14, Q21.** Kept below with their answers, because
the reasoning is usually the useful part. **Still open: Q1, Q7, Q10, Q15, Q17, Q18, Q23, Q24.**

---

## Q1. Does a moving finger on bare copper read cleanly?

**Blocks:** committing a faceplate. **Status: OPEN, and narrower than originally written.**

**Revised 2026-08-06.** This was originally "scan rate and jitter across 4 sliders" and flagged
as blocking everything. Two thirds of it closed on arithmetic. What is left is a different and
more specific question.

### Closed: scan rate

TI's CapTIvate guide gives conversion as **2 clock cycles per count at a 2 MHz effective rate,
so 0.5 us per count**. A sensor at 250 conversion counts takes **125 us**. Reference designs
agree: the CAPTIVATE-METAL panel measures everything in **920 us**, another design in under
**2.4 ms**.

Our case, with each pad's 4 elements measured in parallel (one pin from each block, so one
measurement cycle per pad; [pin-allocation.md](../pin-allocation.md)) and 4 pads sequential:

| | |
|---|---|
| 4 pads x 125 us @ 250 counts | **~500 us** |
| x4 for frequency hopping (noise immunity on) | **~2 ms worst case** |
| No overlay allows retuning to fewer counts | **better than both** |

That is a **500 Hz to 2 kHz update rate**, against an audio block rate of 1 kHz (48 samples
@ 48k) and a human gesture bandwidth of roughly 10 Hz. Latency of 2 ms sits far below the
10-20 ms where lag becomes perceptible.

**The 20-33 ms scan periods in TI's demo designs are not measurement limits.** They are power
optimizations for battery-powered buttons that sleep between scans. This instrument is wall
powered and scans back to back.

**[unverified, minor]** The 125 us figure assumes a 4-element pad resolves in one parallel
cycle, which is the entire point of the 4-block architecture. Design Center reports measured
scan time directly, so confirm rather than assume. Also assumed: frequency hopping is 4
sequential passes rather than something overlapped.

### Closed: jitter at rest

Filterable, with room to spare. **Gesture lives at ~10 Hz, jitter lives at hundreds of Hz**,
and the fast scan rate is what creates that separation. An ordinary filter removes the jitter
without touching the gesture, and there are 8+ ms of latency budget to spend on it.

Worth noting *why* the scan rate matters, since it is not the obvious reason: not latency, but
**signal and noise bandwidth separation**. At TI's 30 Hz demo default, gesture and noise would
overlap and no filter could separate them.

### Still open: monotonicity and continuity under a moving finger

**Narrowed 2026-08-06.** The earlier framing of this asked whether the pad reads *accurately*
under a moving finger. Wrong question for this instrument.

**Absolute accuracy is not directly required.** You scrub by listening and adjusting, so the
loop closes through your ears. A smooth nonlinearity reads as a mildly nonlinear scrub and is
indistinguishable from an intentional design choice.

**But the faceplate has printed marks.** The layout puts **13 tick divisions per pad at 18.00mm
spacing**, with crosses on the quarter, half and three-quarter points, plus Greek acrophonic
numerals in the margins. If a finger on a printed cross should land
at the corresponding point in the sample, then **accuracy against those marks is a
requirement**, and that makes **repeatability** a pass criterion.

The distinction matters because only one of the two is fixable:

- **Accuracy** (reading matches the printed mark) is a **lookup table**. Measure once, correct
  forever.
- **Repeatability** (the same physical spot reads the same tomorrow, with a damp finger, played
  by someone else) **cannot be fixed downstream.** There is nothing to calibrate against if the
  target moves.

This is a direct consequence of the pivot in [ADR 0001](../decisions/0001-pivot-to-capacitive-scrubbing.md).
In the shelved Trautonium design **position was pitch**, and a 2% error is a wrong note, which
is instantly audible. **Scrubbing has no equivalent of a wrong note.**

So only three properties matter:

| Property | Why | If it fails |
|---|---|---|
| **Monotonicity** | Forward finger movement must never report backward, even briefly | Sample stutters backward mid-gesture. Audible. |
| **Continuity** | No dropouts or sudden jumps | Discontinuity in the read pointer is a click. |
| **Stability within a stroke** | No sudden change of character mid-drag | Scrub audibly changes behaviour halfway along. |
| **Repeatability** | Printed marks on the faceplate must correspond to fixed points in the sample | Marks drift against the sound. Not correctable. |

**Everything else is inaudible or calibratable.** Linearity and endpoint offset are both
lookup-table problems: a repeatable error, however large, is correctable.

### Why the geometry helps here

**Position comes from the ratio of copper between the top and bottom bars, not from absolute
capacitance** ([ADR 0003](../decisions/0003-comb-pad-rx0-wraparound.md)). Skin moisture,
contact pressure and contact patch area all scale both bars together, so they **largely cancel
in the ratio.** The ratiometric encoding was chosen for linearity, but it happens to buy
exactly the robustness that repeatability needs.

**The ends are the weak spot.** A large finger's centroid physically cannot reach as close to
the pad edge as a small one, so endpoint trim is **finger-size dependent** in a way the middle
region is not. This is the one genuinely person-varying term.

**If the OLED draws a waveform with a playhead**, a positional bow makes the visual disagree
with what you hear. Same lookup table fixes it.

### Consequences for the faceplate

1. **Extend copper past the printed scale.** The design state offered two options: mark the
   usable region inside the copper, or extend copper past the printed scale. **Printed marks
   settle it: extend the copper**, so every division sits in the well-behaved middle region and
   none land in the finger-size-dependent trim zone at the ends.
2. **Multi-point calibration, not just `Lower_Trim` / `Upper_Trim`.** Two-point trim corrects
   the ends and leaves the middle free to bow. If the centre cross must land on the halfway
   point of the sample, calibrate against several known marks and interpolate between them.
   **The three crosses at 1/4, 1/2 and 3/4 are the natural calibration points**, and they are
   also what a player aims for, so they are where accuracy matters most.
3. **Do not chase better than ~2mm.** Placing a finger on a printed cross, a player's own
   contact centroid is a couple of millimetres from where they think it is. Sensor precision
   beyond that is invisible.

### Why this is still worth testing

Bare copper sits outside TI's validated envelope. **Every TI reference design assumes 1.5-4mm
of plastic** between finger and copper. Direct ENIG contact changes things their tuning
guidance does not cover:

- Contact patch area changes with pressure and drag speed
- Skin moisture varies the coupling, between people and across a session
- Partial galvanic contact rather than clean capacitive coupling through a dielectric

Any of those could in principle produce **momentary reversals or dropouts**, which are the two
things that cannot be fixed downstream. Smoothing cannot help: an artifact that moves with the
finger sits inside the gesture band, and a filter wide enough to remove it also removes the
gesture. Averaging harder only adds lag while keeping the error.

**How to close.** Single-pad test board, [next-steps.md](next-steps.md) step 0. **Do not
measure linearity.** Drag a finger and log position against time, then check:

1. Is the sequence ever non-monotonic during a steady forward drag?
2. Are there dropouts or jumps rather than a continuous trace?
3. Does either get worse with a damp finger, light pressure, or a fast drag?

Then the **repeatability** test, which is now a pass criterion because of the printed marks:

4. Mark a fixed physical spot mid-pad. Touch it 20 times and record the **spread** of readings.
5. Repeat with a damp finger, with light and firm pressure, and with **at least two different
   people** (finger size is the variable that does not cancel in the ratio).
6. Repeat near each end, where trim is finger-size dependent, to find how much of the pad has
   to be excluded from the printed scale. **Drawn at 6mm a side** (generator `scale_inset_mm`,
   2026-09-29); if a large finger centred on an end tick reads short, raise it and re-run
   `hardware/faceplate/design/mkface.py`. It moves only the printed marks.
7. **The gold face** ([ADR 0013](../decisions/0013-gold-face-mask-ink.md)) is ground 1.9mm
   from every pad edge, and over the fan-in lines under the via patch. Compare a pad's
   baseline, sensitivity and noise against the bare test pad, and try a hand resting on the
   right margin while a pad is played. If it costs too much, widen `pad_frame_mm` (one number in the
   generator; `mkface.py` and the checks follow).

**Pass:** spread under ~2mm mid-pad, and monotonic and continuous throughout. Bend in the
curve does not matter; scatter does.

**Expected outcome: fine, or fixable with a calibration table.** TI demonstrated 300mm on four
electrodes, and no overlay gives a *larger* signal delta than their reference designs. The
argument for spending $50 first is not that failure is likely, it is that this is the only
open question where a bad answer costs a faceplate respin instead of a firmware commit.

---

## Q7. Production quantity sourcing

**Blocks:** any run beyond prototypes.
**Status: OPEN, deferred by decision.** A cash question, not a technical one.

| Part | LCSC stock |
|---|---|
| MSP430FR2675TPTR (C2052972) | **10** |
| 2.42" SSD1309 SPI (C5139768) | **27** |

Both are prototype quantities. LCSC-Reels (1000) is the production path on the MSP430 but is a
real cash commitment. The display is a commodity format widely available outside LCSC, so
second-source it.

---

## Q10. OLED dead under bootloader

**Blocks:** nothing yet. **Test before it is load-bearing.**
**Status: OPEN.**

A 2022 report on Daisy Patch showed audio working but the OLED dead under both `BOOT_QSPI` and
`BOOT_SRAM`. May be fixed. This design has both a display and the bootloader, so verify that
combination early rather than discovering it late.

---

## Q19. What is the analog resample round-trip latency?

**Blocks:** sample-accurate loop sync on resampled material. See [workflow.md](../workflow.md).
**Status: OPEN. Must be measured, not assumed.**

Resampling leaves through the DAC, crosses the LPG, and returns through the ADC. The delay is
codec group delay plus at least one audio block, and it puts a **constant offset on the start
of every resampled loop**.

Constant means correctable, so this is not a threat to the design. The risk is **assuming it is
negligible**, because the entire sync scheme rests on loops sharing exact sample boundaries. A
few milliseconds of uncorrected offset is audible as flam against the loop it came from.

**How to measure:** record a click through the resample path, cross-correlate against the
source, report the lag in samples. Do it at the final block size, because block size is part of
the answer. Bake the result in as a compile-time constant and re-measure if the block size or
sample rate ever changes.

---

## Q20. Can a channel resample into itself?

**Blocks:** the resample UI. See [workflow.md](../workflow.md).
**Status: OPEN. A design choice, not a discovery.**

With the source switch on resample, a destination channel that is still playing into the mix
feeds its own output back through the LPG into its own input. That is **real feedback through
an analog path**, and with the gate open it runs away.

| Option | Effect |
|---|---|
| Forbid it | Mute the destination during capture. Safe, predictable, less fun. |
| Allow it | The gate closing limits it. Arguably the correct Buchla-ish answer. |
| Allow with guardrail | Permit it, but do not let the default state be a screaming board. |

Whichever is chosen, **the default state on power-up should not be the runaway one.**

---

## Q22. Does the FR2675 clock need a crystal for reliable UART?

**Blocks: nothing yet, but it decides whether I2C is needed as insurance.**
**Status: LIKELY RESOLVED by adding a crystal.**

The one real failure mode for UART is clock disagreement: neither end is told the baud rate,
each counts on its own clock, and if the MSP430 drifts far enough the link produces garbage.
I2C does not have this problem because the master supplies the clock on a wire.

From the **FR2676/FR2675 datasheet, SLASEO5D**:

- On-chip 16MHz DCO with FLL, **"±1% accuracy with on-chip reference at room temperature."**
  Good enough at 25 degrees. Less reassuring across a full temperature range.
- **XT1 low-frequency crystal oscillator is supported**, and on the **PT package XIN is pin 47
  and XOUT is pin 46**. Both are **unassigned in our design.**

**A 32.768kHz watch crystal and two load caps, roughly $0.20, removes the risk entirely.**
Lock the FLL to XT1 and baud accuracy stops being a question. TI's own CapTIvate power tables
list XT1 alongside REFO as a clock source, so it is a supported configuration for touch too.

**Consequence: the original reason for carrying I2C goes away**, and with the
touch link back on UART the crystal is doing real work rather than being
insurance. Fit the footprint; populating it is a 20 cent decision made later.

**2026-09-28: in the faceplate schematic.** `Y1` is an Epson FC-135 32.768kHz 12.5pF
(`Q13FC13500004`, LCSC C32346, the only Basic 32.768kHz crystal at JLC; C0 1pF against TI's
1.6pF max), on pins 47/46 with 22pF C0G to ground each (SLASEO5D Figure 10-2 for the topology;
the value is 12.5pF less TI's 1pF integrated CL,eff, doubled, rounded to the nearest Basic
part). Whether it is populated is still open.

---
---

# Resolved

## Q21. Do the BSL's fixed pins match our chosen runtime UART pins?

**RESOLVED 2026-09-27: yes. Runtime UART and BSL are the same two wires, pins 4 and 5.**

SLAU550AB does not list pins. §3.1 sends you to *"the Bootloader (BSL) section of each
device-specific data sheet"*. That section of the device data sheet, **SLASEO5D Table 9-4 "UART BSL Pin Requirements and
Functions"**, gives **P1.4 = data transmit, P1.5 = data receive** (and Table 9-5 gives the
I2C BSL as P1.2 SDA / P1.3 SCL). Figure 7-1 puts P1.4/P1.5 on **PT pins 4 and 5**, the
default UCA0 mapping the runtime UART already uses.

**The remapped 44/45 fallback is dropped.** It only ever covered the BSL being on other
pins. It also had nowhere to go: `J12` was built with all ten positions spoken for, five
signals and five grounds.

**One thing taken from SLAU550 §3.3.2.1:** P1.4/P1.5 are also TCK/TMS, and floating TCK/TMS
raise the odds of landing in JTAG mode during the entry sequence. The faceplate puts a 47k
pull-up on each, which also stops RXD floating while the Daisy boots. The 1nF pull-downs TI
pairs with them are left off; they target the hardware entry sequence, which production
does not use. Bring-up still checks that the blank chip answers on these pins.

The history below is kept for the reasoning.

Verified from **SLAU550AB** (MSP430 FRAM Devices Bootloader), September 2022:

- **BSL pins are factory-programmed in the TLV device descriptor and cannot be changed.**
  Section 3.6: *"The configuration data in the TLV is factory programmed and cannot be
  changed."* The user-configurable area (Table 3-2) only selects the **interface** and the
  **I2C slave address**. It does not move pins.
- **The BSL supports UART and I2C, and auto-detects between them by default.** Table 3-2,
  bits 1-0: `00b = Automatic detection of UART or I2C BSL communication`, `01b` UART only,
  `10b` I2C only. FR267x carries a `B5` BSL, and `0xB0-0xBF` means *combined eUSCI I2C and
  UART*.

**The problem this creates.** We chose the **remapped** UCA0 for runtime UART (P5.2 TXD /
P5.1 RXD, pins **45 / 44**) because the default mapping's pin 4 also carries VREF+ and TCK.
**Factory-fixed BSL pins are almost certainly the default mapping**, which for UCA0 is
P1.4 / P1.5, pins **4 / 5**. If so, the connector reaches the runtime UART but **not the
BSL UART**, and [ADR 0005](../decisions/0005-bsl-over-daisy-uart.md) does not work as drawn.

**The consolation, and it is a real one.** Our I2C choice is **UCB0 default** (P1.2 SDA /
P1.3 SCL, pins **14 / 15**), which *is* the default mapping. **If BSL uses defaults, our I2C
pins already match the BSL's I2C pins.** That inverts the original reasoning: I2C is not the
fallback, it may be the *working* BSL path.

**PROPOSED RESOLUTION 2026-08-09: use the DEFAULT UCA0 mapping for runtime too.**

The touch link went back to UART (see [pin-allocation.md](../pin-allocation.md),
"why the touch link is UART"). If runtime UART sits on the **default** P1.4/P1.5,
pins 4 and 5, then **runtime and BSL are the same two wires** and the whole
question dissolves rather than being answered.

The original objection to pins 4/5 was that pin 4 also carries **TCK** and
**VREF+**. Neither bites here: **SBW is 2-wire on TEST/RST so 4-wire JTAG and its
TCK are unused**, and CapTIvate does not need VREF+.

**Still to confirm on the bench**, and only then close this: that BSL really does
answer on pins 4/5, and that nothing about pin 4's shared functions interferes.
**Route the remapped pins 44/45 as well** as a fallback. Copper is free now and a
respin is not.

---

## Q2. eUSCI_A / eUSCI_B pin muxing on the FR2675 PT package

**RESOLVED 2026-08-06.** Datasheet SLASEO5D (revised September 2021), Table 7-2, PT column.

**They do not share pins. No 0R jumpers needed.** Route both UART and I2C, select in software
via the `USCIA0RMP` / `USCIBxRMP` bits in `SYSCFG2` / `SYSCFG3`.

| Interface | Mapping | PT pins |
|---|---|---|
| **UART (use this)** | UCA0 remapped, P5.2 / P5.1 | **45 / 44** |
| **I2C (use this)** | UCB0 default, P1.2 / P1.3 | **14 / 15** |

**Two traps found while checking.** CapTIvate electrodes occupy pins 23-30 and 32-39, and all
16 are used by our four pads. That makes two obvious-looking mappings unusable:

- **UCA1 UART** (pins 30 / 29) collides with **CAP1.3 and CAP1.2**
- **UCB1 default I2C** (pins 38 / 39) collides with **CAP3.2 and CAP3.3**

Picking either by habit gives a board that can neither talk nor sense.

Full table in [../pin-allocation.md](../pin-allocation.md).

---

## Q3. Reconcile the two IO plans

**RESOLVED 2026-08-06, then reopened and re-resolved the same day.** Settled as **12 ADC
routed, 10 populated, no mux**:

- 2 pots per channel (8 total) on **CV_1-CV_8**
- 4 more on **A2, A3, D8, D9**. Populate 2 of them now, leave 2 as stuff options.
- No CV or gate jacks into the Daisy, and **no panel USB**
- Encoder on the main PCB
- CV_OUT_1 / CV_OUT_2 drive the LPG, one envelope per stereo side

**The first answer here was 10 pots, and it was wrong.** It rested on two claims that did not
survive checking, both corrected under [Q14](#q14-are-a8a9-really-reserved-for-dfu-and-usb-midi):
that A8/A9 were needed for DFU and USB MIDI, and that D9 was the only SPI2_MOSI pin available.
PB15 (A9) is also SPI2_MOSI, so moving the OLED there freed D9, and relocating the IRQ to A8
freed D8.

**13 is impossible.** All 12 ADC-capable pins are in use, and a CD4051 costs 3 GPIO for its
select lines, of which there are zero spare.

**The budget closes because three functions moved off bidirectional GPIO.** This design leaves
the gate pins idle, since there are no jacks:

- **BSL RST and TEST -> B5 and B6** (GATE_OUT_1/2). Plain `GPIO` in libDaisy, and these are
  Daisy-driven outputs. **Needs a 5V to 3.3V divider**, see Q13 below.
- **Encoder push -> B9** (GATE_IN_2). Input-only is all a button needs.
- **OLED RST -> RC/pullup**, no GPIO.

Result: 14 of 14 bidirectional GPIO used, BSL retained, and the data-ready IRQ retained on D8.
Keeping the IRQ matters: polling costs latency in the touch path.

**A mux does not help.** CD4051 spends 3 GPIO on select lines to save 8 ADC pins, but the pots
that cost nothing are already on CV_1-8 (input-only pins that can do nothing else). Only pots
9+ cost GPIO, and there are two. It would spend 3 to save 2.

---

## Q4. Does the Daisy bootloader hardcode 4-bit SD?

**RESOLVED 2026-08-05.** No, and the concern was backwards.

`DaisyBootloader/shared/bootloader.cpp:164` (HEAD `8b279a8`):

```cpp
sd_cfg.width = SdmmcHandler::BusWidth::BITS_1;
```

It is libDaisy's `Config::Defaults()` that is 4-bit @ 50MHz; the bootloader explicitly
overrides to 1-bit. **SD-card firmware drops work on 3-pin wiring.**

**Decision: use 1-bit.** Saves 3 GPIO (D2, D3, D4 freed), and samples load into SDRAM at boot
rather than streaming, so bandwidth only affects a boot-time delay of a second or two.

---

## Q5. RoHS / cadmium status on vactrols

**CLOSED 2026-08-06.** Vactrol supply handled directly. No further action.

---

## Q6. 4P3T panel-mount toggle availability

**RESOLVED 2026-08-06.** Moot: the mode switch is now **two positions**, stereo VCF or stereo
VCA, not three.

That is a **DPDT** (one pole per stereo side), which is a commodity part. No 4P3T hunt, no
rotary fallback, no panel-layout risk. See
[ADR 0007](../decisions/0007-buchla-lpg-over-serge-vcfq.md).

---

## Q8. Is Patch SM D8 (MISO) actually free?

**RESOLVED 2026-08-05.** Yes. `libDaisy/src/dev/oled_ssd130x.h` sets the SPI transport to:

```cpp
spi_config.periph_direction = SpiHandle::Config::Direction::TWO_LINES_TX_ONLY;
spi_config.pin_config.miso  = Pin(PORTX, 0);   // unused-pin sentinel
```

Write-only confirmed, MISO explicitly unused. **D8 is free**, and after the Q14 correction it
carries **pot 12** (the MSP430 data-ready IRQ moved to A8).

---

## Q9. libDaisy SSD130x `Update()`, blocking or not?

**RESOLVED 2026-08-05.** The DMA path is live. The design state's concern is stale for this
revision.

`Update()` branches on `useDma_` and calls `TransferPageDma(0)`, which calls
`transport_.SendDataDma(...)` at line 646 with `SpiPageCompleteCallback` chaining page to page.
The commented-out line at 650 is a leftover debug variant two lines below the real call.

At 1KB per frame it barely mattered either way.

---

## Q11. LGE108 vs CGS108 topology

**CLOSED 2026-08-06.** Moot. The analog section is **Eddy Bergman's Buchla-style LPG, doubled
for stereo**. Serge VCFQ is not being revisited, so the CGS108 / LGE108 question is academic.
Reasoning retained in [ADR 0007](../decisions/0007-buchla-lpg-over-serge-vcfq.md).

---

## Q12. FR2675 symbol and footprint in EasyEDA/LCSC library

**RESOLVED 2026-08-06.** Using the **LCSC part C2052972 (MSP430FR2675TPTR)** schematic symbol
and footprint. Verify the footprint against the datasheet PT package drawing before ordering,
which is a 10-minute check that prevents a dead board.

---

## Q14. Are A8/A9 really reserved for DFU and USB MIDI?

**RESOLVED 2026-08-06. No, and the original documentation was wrong.** This cost two usable
pins and capped the design at 10 pots until corrected.

**Patch SM has two independent USB ports.** Verified against the Rev3 schematic
(`ES_Daisy_Patch_SM_Schematic.pdf`, 2024-02-08) and libDaisy source:

| Port | Peripheral | Pins | On the header? | libDaisy role |
|---|---|---|---|---|
| **Onboard Micro USB** | USB_OTG_FS | PA11 / PA12 (+PA9 VBUS) | **No.** On the module. | `usbd` = **device**: DFU, USB MIDI |
| **A8 / A9** | USB_OTG_HS | PB14 / PB15 | Yes | `usbh` = **host**: USB drives |

Evidence:

- The schematic shows a **Micro USB connector on the module**, netted `USB_OTG_FS_D_+/-`,
  `USB_OTG_FS_VBUS`, `USB_OTG_FS_ID`, with the note that it "allows for powering of the MCU
  from just USB (allowing for pre-flashing, etc. without having to have it powered by
  eurorack)". The header separately carries `USB_HS_DP` / `USB_HS_DM`.
- `libDaisy/src/usbd/usbd_conf.c` (device mode) configures `USB_OTG_FS` on `GPIOA`
  `GPIO_PIN_11 | GPIO_PIN_12`, plus PA9 for VBUS.
- `libDaisy/src/usbh/usbh_conf.c` (host mode) configures `GPIOB` `GPIO_PIN_14 | GPIO_PIN_15`
  with `GPIO_AF12_OTG2_FS`.
- `DaisyBootloader` default (`#if !DSY_DFU_USE_EXT_USB`) runs DFU on FS and initialises USB
  **host** on the external port to read firmware from a drive.

**Decision: spend A8/A9 on IO.** Given up: panel USB jack, firmware-from-USB-drive, future USB
MIDI host. Kept: DFU over the onboard Micro USB, SD card firmware drop, USB MIDI device.
The practical cost is that **USB access means unscrewing the module from the rack.**

**Build the bootloader without `DSY_DFU_USE_EXT_USB`**, which would move DFU to a port this
board no longer wires.

---
---

# New, opened by the pin allocation work

## Q13. Do the gate outputs drive BSL cleanly through a divider?

**Blocks:** nothing.
**Status: CLOSED 2026-09-06, by deletion — there is no divider.**

SLAU550 Rev AB §3.3.3: the FR26xx boot code does **blank device detection** and jumps
straight into the BSL when the reset vector reads 0xFFFF, which *"eliminates the need for two
additional wires (TEST, RST)"*. A chip off the reel answers over the UART on its own, so the
hardware entry sequence is never used, and `R26`-`R29` are deleted. `B5`/`B6` are gate
outputs. The original reasoning is kept below because the failure mode it describes is still
the one to expect if BSL ever misbehaves.

**Replaced by a different watch item:** SLAU550 §3.4, the BSL **ten-second time-out** into
LPM4. See [ADR 0005](../decisions/0005-bsl-over-daisy-uart.md).

Gate outputs are **0-5V** (Patch SM datasheet Table 3) and the **MSP430 I/O absolute max is
DVCC+0.3V = 3.6V**. RST and TEST each need a **5V to 3.3V divider**, two resistors per line.

The datasheet gives output impedance (100R) but **not the internal topology of the gate output
stage**. Confirm on the bench that B5/B6 toggle cleanly as GPIO through the divider.

**Why this matters more than it looks:** BSL entry needs **two clean rising edges on TEST while
RST is held low**, and the single most common BSL entry failure is exactly "fewer than two
rising edges". Mushy edges from the divider would present identically to a protocol bug, and
you would chase it in the wrong place.

**How to close:** scope B5/B6 at the MSP430 pin with the divider fitted, before writing any BSL
code.

## Q15. Does A9 drive the OLED cleanly as SPI MOSI?

**Blocks:** the display, and with it pots 11-12.
**Status: OPEN.** Prototype bench check.

**PB15 (A9) is a supported SPI2_MOSI pin**, confirmed in `libDaisy/src/per/spi.cpp:741`
alongside PC1 and PC3, all `GPIO_AF5_SPI2`. `SpiHandle` accepts it with no custom code.

The open part is analog, not software. **A9 is normally USB_HS_DP**, and the module may carry
ESD protection or common-mode filtering on those lines whose capacitance could soften SPI
edges. At SSD1309 clock rates this should be a non-issue, but it is worth ten minutes.

**How to close:** drive the display from A9 on the first prototype and scope MOSI at the panel
connector. If the edges are poor, drop the SPI clock first, since 1KB per frame leaves plenty
of headroom.

**If it fails:** MOSI returns to D9 and the design falls back to 11 pots, with pot 11 on D8.
No respin required if the pot footprints are already there, which is the argument for routing
all 12 and populating 10.

---

## Q17. How tight can the inter-pad gap be?

**Blocks:** crosstalk between adjacent pads. Vertical spacing only.
**Status: OPEN**, but **de-risked**, and cheap to answer alongside the test board.

**Promoted then demoted, both on 2026-08-06.** It was briefly the highest-leverage hardware
question, because the reference composition appeared to lock `pad length = 12 x pad pitch`,
which would have made the gap set the size of the whole instrument.

**That ratio turned out to be an artefact.** The reference sketch drew pads as single strokes
with no thickness, so the 420/35 measurement described the drawing, not a design intent. Pad
length and gap are now independent, and the gap costs nothing but blank panel.

**The layout uses an 8mm gap with 10mm pads**, settled for the faceplate PCB on 2026-09-27
([ADR 0003](../decisions/0003-comb-pad-rx0-wraparound.md)). It was 9mm until the panel shrink
took 1mm off each gap. That is close to the design state's **>=10mm closest approach**
guidance, where the earlier 6mm was well under it, and a bad answer here is much less
expensive than it looked. The faceplate does not answer this question; it only has to live
with it.

**Still worth measuring**, because a grounded guard strip might permit tighter spacing if the
layout ever wants it back (the faceplate now has one: 4mm of grounded gold between the pads'
frames, [ADR 0013](../decisions/0013-gold-face-mask-ink.md)), and because nobody has confirmed the >=10mm figure applies to
parallel pads at all (it was written for the diagonal layout where pads converge at a point).
See [../panel-budget.md](../panel-budget.md).

Four pads at 12mm plus three gaps at 10mm consume **78mm** of panel height. **The 10mm figure
is an extrapolation**, taken from the design state's ">=10mm closest approach" guidance which
was written for the *diagonal* layout, where pads converge at a point. Parallel pads sit at
closest approach along their whole length, so the requirement may differ in either direction.

**A grounded guard strip between pads may allow a tighter gap.** Across three gaps this is worth
up to 30mm of panel height, which is the difference between a comfortable layout and a cramped
one.

**How to close:** lay out **two** pads on the single-pad test board instead of one, at two or
three candidate gap widths, with and without a guard strip. Measure crosstalk. Nearly free,
since the board is already being fabricated for [Q1](#q1-does-a-moving-finger-on-bare-copper-read-cleanly).

See [../panel-budget.md](../panel-budget.md).

---

## Q18. What is the OLED module's outline height?

**Blocks:** the upper strip of the panel budget.
**Status: OPEN.** Datasheet check, ten minutes.

The design state records only the **active area**: 55.01 x 27.49mm. These are **bare panels with
an FPC tail**, so the glass outline is larger. The panel budget currently assumes **~40mm**,
which is an estimate and exceeds the entire strip left by the pads on the old 219 x 110mm board.

**How to close:** pull the mechanical drawing for LCSC C5139768 (HS242L01W4S01) and record the
glass outline plus the FPC tail's bend radius and connector position.

---

## Q16. Does the SSD1309 need CS toggling?

**Blocks:** nothing. Recorded as a known fallback.
**Status: OPEN, not currently needed.**

The budget closes with CS on D1, so this is not on the critical path. But if a pin is ever
needed, SSD1309 in 4-wire SPI generally tolerates **CS tied permanently low** when it is the
only device on the bus. Some SSD130x controllers use CS edges to resync the command/data state
machine. Test before relying on it.

---

## Q23. Keep the UART quiet while the pads are being scanned

**Blocks:** nothing in hardware; it is a firmware rule the faceplate layout depends on.
**Status: OPEN** (raised 2026-09-28, faceplate layout).

`J1` is fixed by the main board in the gap between pads 3 and 4, and its signal row sits on
the back behind pad 4's top edge. No routing moves that. So the UART must not toggle during
a CapTIvate conversion: the MSP430 holds its reports until a scan is done, and the Daisy
only transmits when asked (request/response), so `MSP430_RXD` is idle while the pads are
being measured. The lines themselves run in the gap over an L3 ground strip, away from the
pad copper.

**How to close:** write it into the protocol when the touch firmware is written, then check
on the bench that no conversion ever overlaps a frame (scope `MSP430_TXD` / `MSP430_RXD`
against a GPIO toggled around the scan).

---

## Q24. Is a trace under same-pad, same-cycle elements really shielded?

**Blocks:** confidence in the faceplate's L2 routing, not the routing itself.
**Status: OPEN** (raised 2026-09-28).

The faceplate brings each pad's four lines to the right margin under their own pad on L2:
RX1's bus runs on under the RX3 bars, RX2's under zone 4's RX0, and RX0's join under RX2.
The argument that this is harmless is that a pad's four elements are one pin from each
CapTIvate block, measured in the same cycle and driven with the same waveform, so to a
trace below them they act close to a driven shield (ADR 0003, "Connecting the bars"). That
is reasoning, not a TI statement.

**How to close:** find it in the CapTIvate Technology Guide (parallel scanning / mutual
capacitance between elements of one sensor) or measure it on the first board: a finger
over zone 4 must not move RX1's count more than over any other non-RX1 zone.
