Dylan-Hackett/vuulgaris-v1/docs/decisions/0005-bsl-over-daisy-uart.md

# 0005 - Daisy flashes the MSP430 over BSL, no per-unit programmer

**Status:** Accepted
**Date:** pre-2026-08-05 (recorded retroactively from design state section 4)

## Decision

JLC solders a blank MSP430FR2675 from the reel. The **Daisy flashes it over the UART that
is already routed** between the boards, using the BSL in secure ROM.

Verified in TI SLAU550 device table: MSP430FR2675, BSL version **00.09.36.B5**, UART on
eUSCI_A, I2C on eUSCI_B. Both interfaces supported.

## Hardware cost

**Two extra wires from the Daisy: RST and TEST**, plus a **5V to 3.3V divider on each**.

**Updated 2026-08-06:** these live on **B5 (GATE_OUT_1)** and **B6 (GATE_OUT_2)**, not on
bidirectional GPIO. Gate outputs are plain `GPIO` in libDaisy and RST/TEST are Daisy-driven
outputs, so they fit there, and this design leaves the gate pins idle. That is what kept this
decision affordable when the pin budget tightened. See
[ADR 0009](0009-io-plan-12-adc.md).

> ### SUPERSEDED 2026-09-06 — there is no hardware cost. Zero wires, zero resistors.
>
> **SLAU550 Rev AB §3.3.3 / SLAU610D §3.3.3, verbatim:** *"The boot code on the **FR26xx**,
> FR25xx, FR24xx, and FR23xx MCUs supports blank device detection to avoid the BSL entry
> sequence. This saves time and also **eliminates the need for two additional wires (TEST,
> RST)** for the BSL invocation sequence... The device jumps directly to the BSL and bypasses
> the entry sequence only when the reset vector has a value of 0xFFFF."*
>
> The FR2675 is an FR26xx part and a chip off the reel has a 0xFFFF reset vector by
> definition, so **it lands in the BSL by itself and answers over the UART.** The hardware
> entry sequence is not needed for the first flash, and software invocation
> ([pin-allocation.md](../pin-allocation.md)) covers every flash after it.
>
> `R26`-`R29` and both dividers are **deleted**. `GATE_OUT_1`/`GATE_OUT_2` are real gate
> outputs again; `GATE_OUT_2` now drives the BBD inhibit. This also closes
> [Q13](../notes/open-questions.md) ("do the gate outputs drive BSL cleanly through a
> divider?") by deletion — there is no divider.
>
> **The one thing to design around: §3.4, the BSL time-out.** *"If no communication has been
> established within ten seconds, the device enters LPM4 mode. To invoke the BSL again, the
> device power must be cycled, or a reset or NMI must be received."* On a blank chip the Daisy
> has **ten seconds from MSP430 power-up** to say something. Miss it and the recovery is a
> power cycle, because nothing on the main board drives RST any more. That is acceptable for a
> one-time factory step; if it ever needs to be automatic, put RST on **A9** (native 3.3V, no
> divider) rather than back on a gate output.

**Gate outputs are 0-5V** and the **MSP430 I/O absolute max is DVCC+0.3V = 3.6V**, so each
line needs a divider (two resistors, four total). **Bench-verify the edges before writing BSL
code:** entry depends on two clean rising edges on TEST, and mushy edges from the divider
present identically to a protocol bug. See `../notes/open-questions.md` Q13.

## Gotchas, in the order you will hit them

- **Entry sequence:** RST/NMI held low while pulling TEST high and applying the next two
  edges (falling, rising). BSL starts after TEST is held low and RST is released. TI
  documents the failure modes; the common one is **fewer than two rising edges on TEST
  while RST is low**. Expect to lose a day here with a logic analyzer.
- **Wait ~300ms after entry invocation before the first command.** This BSL version is slow
  to initialise. Skipping the wait looks exactly like a hardware fault.
- **Password = contents of the interrupt vector table (FFE0h-FFFFh).** All FFs on a fresh
  chip; becomes your vectors after flashing. Wrong password with mass erase enabled wipes
  the chip and you start over. Recoverable.
- **Known doc bug:** SLAU550 page 18, the I2C unlock example shows length field `0x33`
  where it should be `33` decimal. If I2C will not unlock, check this first.

## Brick risk: essentially zero if you do not go looking for it

BSL code is in secure ROM and cannot be overwritten. TI states that even if the device is
secured by disabling JTAG, the BSL still works.

**The one permanent brick is deliberately disabling BSL *and* locking JTAG.** TI's forum
confirms that with BSL disabled completely you cannot regain access.

**Rule: leave JTAG/SBW unlocked and BSL enabled. Do not touch the security settings.**

**Put 4 SBW test pads on the board regardless** (TEST, RST, 3V3, GND). Free, and it is the
recovery path: a $12 MSP430 LaunchPad's eZ-FET can flash through them.

## Also on the board: the PGMR connector

**Put the CAPTIVATE-PGMR connector on the faceplate PCB.** The Design Center cannot talk to
an MSP-FET or a LaunchPad eZ-FET; the PGMR carries a separate MSP430F5528 running HID
Bridge firmware that streams live sensor data to the PC. That live data view is the entire
point: jitter, scan time, linearity, trim.

> **REVISED 2026-09-28: the PGMR connector is `J1`, the cable header. Nothing is added.**
> TI's CAPTIVATE-PGMR chapter (CapTIvate Technology Guide) gives the PGMR a 20-pin connector
> and allows a custom target to use "only the required signals, power and ground using
> wires", under about 20cm. Its UART set is six: +3.3V, GND, SBWTCK_TST, SBWTDIO_RST,
> UART-TXD, UART-RXD. `J1` already carries exactly those six. To tune, pull the ribbon off
> the main board's `J12` and jumper its socket to the PGMR:
>
> | ribbon pin | signal | PGMR 20-pin |
> |---|---|---|
> | 1 | `MSP_TEST` | 10, SBWTCK_TST |
> | 3 | `MSP_RST` | 9, SBWTDIO_RST |
> | 5 | `MSP430_RXD` | 7, HID bridge UART TXD |
> | 7 | `MSP430_TXD` | 8, HID bridge UART RXD |
> | 9 | `P3V3_MSP430` | 18, +3.3V to target |
> | 2 | GND | 19, GND |
>
> Why not a header on the faceplate: its back faces the main board across the 10mm gap and
> cannot be reached assembled; with the ribbon in, the Daisy's TX and the bridge's TX would
> both drive `MSP430_RXD` and the PGMR's LDO would sit on `U6`'s rail. Unplugging the ribbon
> removes both conflicts by construction (TI's own FR2676 module needs isolation jumpers for
> the same reason). The cost: while tuning, the faceplate runs from the PGMR's 3.3V, so noise
> conducted from the main board is out of the loop; the pads, the enclosure and whatever the
> main board radiates are still there.

TI's recommended workflow is exactly this: build the custom sensing board, integrate while
keeping the PGMR connector so Design Center works against real hardware, remove after
testing. Tuning against the actual pads, in the actual enclosure, next to the actual
switching supply is the only tuning that counts. Leave unpopulated on production units.

## Fallbacks if BSL-over-Daisy proves painful

- Distributor pre-programming (Digi-Key / Mouser / Arrow): setup fee plus cents per part,
  standard at volume.
- Pogo-pin test fixture + LaunchPad eZ-FET during board test: cheapest for small batches.
- Gang programmer (MSP-GANG, Elprotronic GangPro430): 8 at a time, worth it in the hundreds.
