Dylan-Hackett/vuulgaris-v1/docs/review/recheck/07-audio-io.md

# 07: Audio IO: headphone, EXT input, jacks, pots

Block: U9/U10, R501-R522 and C501-C512 (the audio ones), RT501-RT504, J2-J10,
RV1-RV6.

Sources: `TI-OPA1688-datasheet.pdf` (SBOS724A: Table 6-1, 7.1, 7.4, 7.5,
8.3.2, 8.3.3 with Figures 8-3/8-4 rendered), `PJ-376-jack.pdf` (SOFNG, rendered),
`PJ-603-jack.pdf` (Haoyu/Legion, image-only, rendered at 500 dpi),
`Alpha-RD902F-40-15R1-dual-9mm-pot.pdf` (drawing RD902F-40-(L)R1-XXX-00D70 and
the spec sheets, all rendered), `ALPS-RK09L1240A12-pot.pdf`,
`Bourns-3224W-trimmer.pdf`, the BOM, and the Patch SM sheet for levels.

## Which pot is on the BOM

The BOM line for RV1-RV4 and RV6 (`fab/vuulgaris-BOM.csv`) has **no LCSC
number** and the note "NOT FROM JLC -- FIT BY HAND. Alpha
RD902F-40-15R1-B100K ... Tayda A-5440"; RV5 likewise with B10K, Tayda A-6433.
The footprint is still named `RES-ADJ-TH_RK09L1240A12`, but the fitted part
is the Alpha, so the check is against **Alpha's drawing**.

Alpha RD902F-40-(L)R1-XXX-00D70, rev -0057 (p2), with the spec sheet (p3-p4)
and taper chart (p5):

- "SHAFT SHOWN IN FULL C.C.W. POSITION". The front view, from the shaft end
  with the pins down, numbers the terminals **1 2 3 left to right**.
- p5 plots "TERM.1-2 OUTPUT VOLTAGE / TERM.1-3 INPUT VOLTAGE" rising from 0 as
  rotation travel goes from "TERM 1" to "TERM 3": **terminal 1 is the CCW end**.
- P.C.B. mounting hole detail: six Ø1.0 holes at 2.5 mm pitch in two rows 2.5
  mm apart, the near row 7.5 mm from the shaft; two tab slots **1.8 x 1.1**,
  11.3 mm over the outside, long side along the line joining them.
- L = 15 for the -15 shaft; M7 x 0.75 bushing; Ø6.35 shaft.

Our footprint, F.Cu, read from the board (RV1 and RV5 identical): tab slots 7/8
at (+-4.75, -5.00), drill 1.8 x 1.1 with the 1.8 along x (the line joining
them), so 4.75 x 2 + 1.8 = 11.3 over the outside; pin rows at y = 2.5
(pads 4, 5, 6) and y = 5.0 (pads 1, 2, 3), i.e. 7.5 and 10.0 from the tab line;
x = -2.5 / 0 / +2.5; Ø1.0 holes. Seen from above, as the front view is, the
shaft is at (0, -5) with the pins below it, and **pads 1 and 4 are on the left:
terminal 1, the CCW end, for both gangs.** **CLEAN.** The drawing does not
say which row is the front gang, and does not need to: both gangs are the same
value and taper and each carries one stereo channel.

Ratings: B taper 0.05 W (p3 1.2). RV1 across 12 V: 1.4 mW. RV5 (10k) with the
wet signal at up to +-9 V: 4 mW rms. Fine. Tracking error is specified only as a
volume control (-40 to 0 dB within 3 dB, p3 1.9), which is what a stereo knob
gets.

## Jacks

### J2-J6, PJ-376 (SOFNG)

Circuit diagram: **#1** is the sleeve (the hooked contact), **#2** the ring
contact, **#3** the tip contact; the plug gauge numbers the plug 1 sleeve,
2 ring, 3 tip. No switch contacts on this part. P.C.B. layout: 1, 2, 3 in line at
3.5 mm pitch, pin 1 nearest the mouth (3.5 / 7 / 10.5 mm from the body face).

| ref.pin | net | source says | ours | verdict |
|---|---|---|---|---|
| J2-J5 .1 | GND | sleeve | GND | CLEAN |
| J2-J5 .2 | GND | ring | GND | CLEAN: a mono jack; a TRS plug's ring is grounded, which is harmless for these signals |
| J2.3 / J3.3 / J4.3 / J5.3 | CVOUT_JACK / GATEOUT_JACK / CV_IN_JACK / GATE_IN | tip | | CLEAN |
| J6.1 / .2 / .3 | GND / HP_OUT_R / HP_OUT_L | sleeve / ring / tip | | CLEAN: tip = left, ring = right |

Library footprint: pads 1/2/3 at x = -3.5 / 0 / +3.5, outline x -12.0 to +4.5,
so the mouth is at -x beyond pad 1, as drawn. Rating 0.5 A, 24 V DC.

### J7-J10, PJ-603 (Haoyu)

The drawing's own SCHEMATIC box settles it without the variant argument:
contact **2** is the sleeve (the line from the barrel), **5** the ring (V
spring), **4** the tip (^ spring), and **3 ends in an arrow resting on 4's
spring**, the normally-closed tip switch. PJ-603-3 (mono) keeps 2, 3, 4; PJ-603-2
(no switch) keeps 2, 5, 4. P.C.B. layout, top view, mouth to the left: 2# on the
centre line 7.6 mm from the face; 3# and 4# on one side at 15.1 and 22.5 mm;
5# opposite 4#, 5 mm away.

| ref.pin | net | source says | ours | verdict |
|---|---|---|---|---|
| J7.2 / J8.2 | GND | sleeve | | CLEAN |
| J7.4 / J8.4 | EXT_IN_L/R | tip | | CLEAN |
| J7.3 / J8.3 | GND | tip switch, closed with no plug | GND | CLEAN: unplugged, the tip (and U10's input) is grounded; a plug lifts the spring off 3 |
| J7.5 / J8.5 | GND | ring | GND | CLEAN for unbalanced sources; a balanced source's cold leg is grounded, which balanced outputs tolerate |
| J9.2 / J10.2 | GND | sleeve | | CLEAN |
| J9.4 / J10.4 | LINE_OUT_L/R | tip | | CLEAN |
| J9.3 / J10.3 | open | tip switch | open | CLEAN |
| J9.5 / J10.5 | GND | ring | | CLEAN |

Library footprint: 3 (0.05, 2.5), 4 (7.45, 2.5), 5 (7.45, -2.5), 2 (-7.45, 0),
outline to x = -24.05 (9 mm barrel + 7.6 mm to pin 2). Spacing 7.5 / 7.4 / 14.9
and 5.0 against the drawing's 7.6->15.1->22.5 and 5: matches the top view.
J7-J10 are on B.Cu and the board copies have local y negated, a genuine flip.
This supersedes review-packet item 3's "beep one jack" caveat: the drawing in
the repo states the contact functions directly.
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
