Dylan-Hackett/vuulgaris-v1/docs/review/recheck/08-footprints.md

# 08: Footprints against manufacturer drawings

Block: every non-passive footprint on both boards, read from the two
`.kicad_pcb` files; the 24 panel parts; part heights against the 10 mm gap
between the boards.

Sources (all in `datasheets/`, rendered with pdftoppm where image-only):
`AMS1117-datasheet.pdf` p7 ("3 LEAD SOT-223 PLASTIC PACKAGE");
`onsemi-MMBFJ113-datasheet.pdf` p1 (package figures), p7-p8 (outlines);
`1N4148W.pdf` p1 (pinning), p3 (SOD-123 outline); `BZT52C3V9-zener.pdf` p1, p4
("Pinning information", "Suggested solder pad layout"); `SMAJ6.0A-TVS.pdf` p5
("Dimensions, DO-214AC (SMA)" with the solder pad figure); `YLED0402Y.pdf` p1
(section 2, "Package Profile & Soldering PAD Suggested"); `Lelon-RVT-electrolytic.pdf`
p2 (size code table and dimension table); `TI-TL072-datasheet.pdf` p77 (D0008A);
`TI-TL074-datasheet.pdf` p59 and `TI-TL084-datasheet.pdf` p52 (D0014A);
`TI-OPA1688-datasheet.pdf` p40 (D0008A); `TI-CD4046B-datasheet.pdf` p12-p13
(NS0016A); `Microchip-MCP23017-datasheet.pdf` p31-p32 (SO 28, 7.50 mm);
`MeanWell-SKM10-DKM10-spec.pdf` p5 (mechanical, bottom view);
`Xvive-VTL5C3-datasheet.pdf` p1 (package dimensions); `Dailywell-2MD1T1B1M2QES-DPDT.pdf`
(drawing 2MD1T1B1M2QES-5, "P.C. MOUNTING"); `BOOMELE-C5665-2x5-box-header.pdf`
("P.C.B Layout"); `hanxia-HX-JN2.54-2x5P-TP-H8.9.pdf` ("RECOMMEND P.C.B LAYOUT
(TOP VIEW)"); `Epson-FC-135-32.768kHz.pdf` p1 (sections 3 and 4);
`TI-TPD1E10B06-datasheet.pdf` p19-p20 (DPY0002A); `TI-MSP430FR2675-datasheet.pdf`
p118-p120 (PT0048A); `PJ-603-jack.pdf`, `PJ-376-jack.pdf` (heights only); the BOM;
`docs/design-state.md` ("Panel part heights"); `hardware/faceplate/README.md` §2, §4, §5.

Footprints already settled against their drawings in earlier sections, and not
repeated here: U1 Patch SM (03), J11 USB-C (02), DS1, J1 microSD, ENC0-ENC8,
SW4-SW9 (04), U101/U201 V3205SD DIP (05), RV1-RV6, J2-J10, RT301-RT504 (07).
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
