Dylan-Hackett/vuulgaris-v1/docs/review/recheck/06-lpg.md

# 06: Low pass gate, both channels

Block: U301/U302, U401/U402, VT301/VT302, VT401/VT402, R3xx/R4xx, C3xx/C4xx,
D301/D401, RT301/RT401, RV1/RV2/RV3, SW1.

Sources: `datasheets/LPG Schematic E Bergman (3) (1).jpg` (6000 x 6000), read in
six zoomed regions plus a separate crop of D1; `TI-TL084-datasheet.pdf`
(SLOS081O), `TI-TL074-datasheet.pdf` (identical file to the TL072 one,
SLOS080W), `Xvive-VTL5C3-datasheet.pdf`, `BZT52C3V9-zener.pdf` (Formosa, image
pages rendered), ADRs 0007 and 0011, `Dailywell-2MD1T1B1M2QES-DPDT.pdf`.
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
