Dylan-Hackett/vuulgaris-v1/docs/reference/V3.0.kicad_sch

## KiCad design docs/reference/V3.0.kicad_sch (2026-09-11)

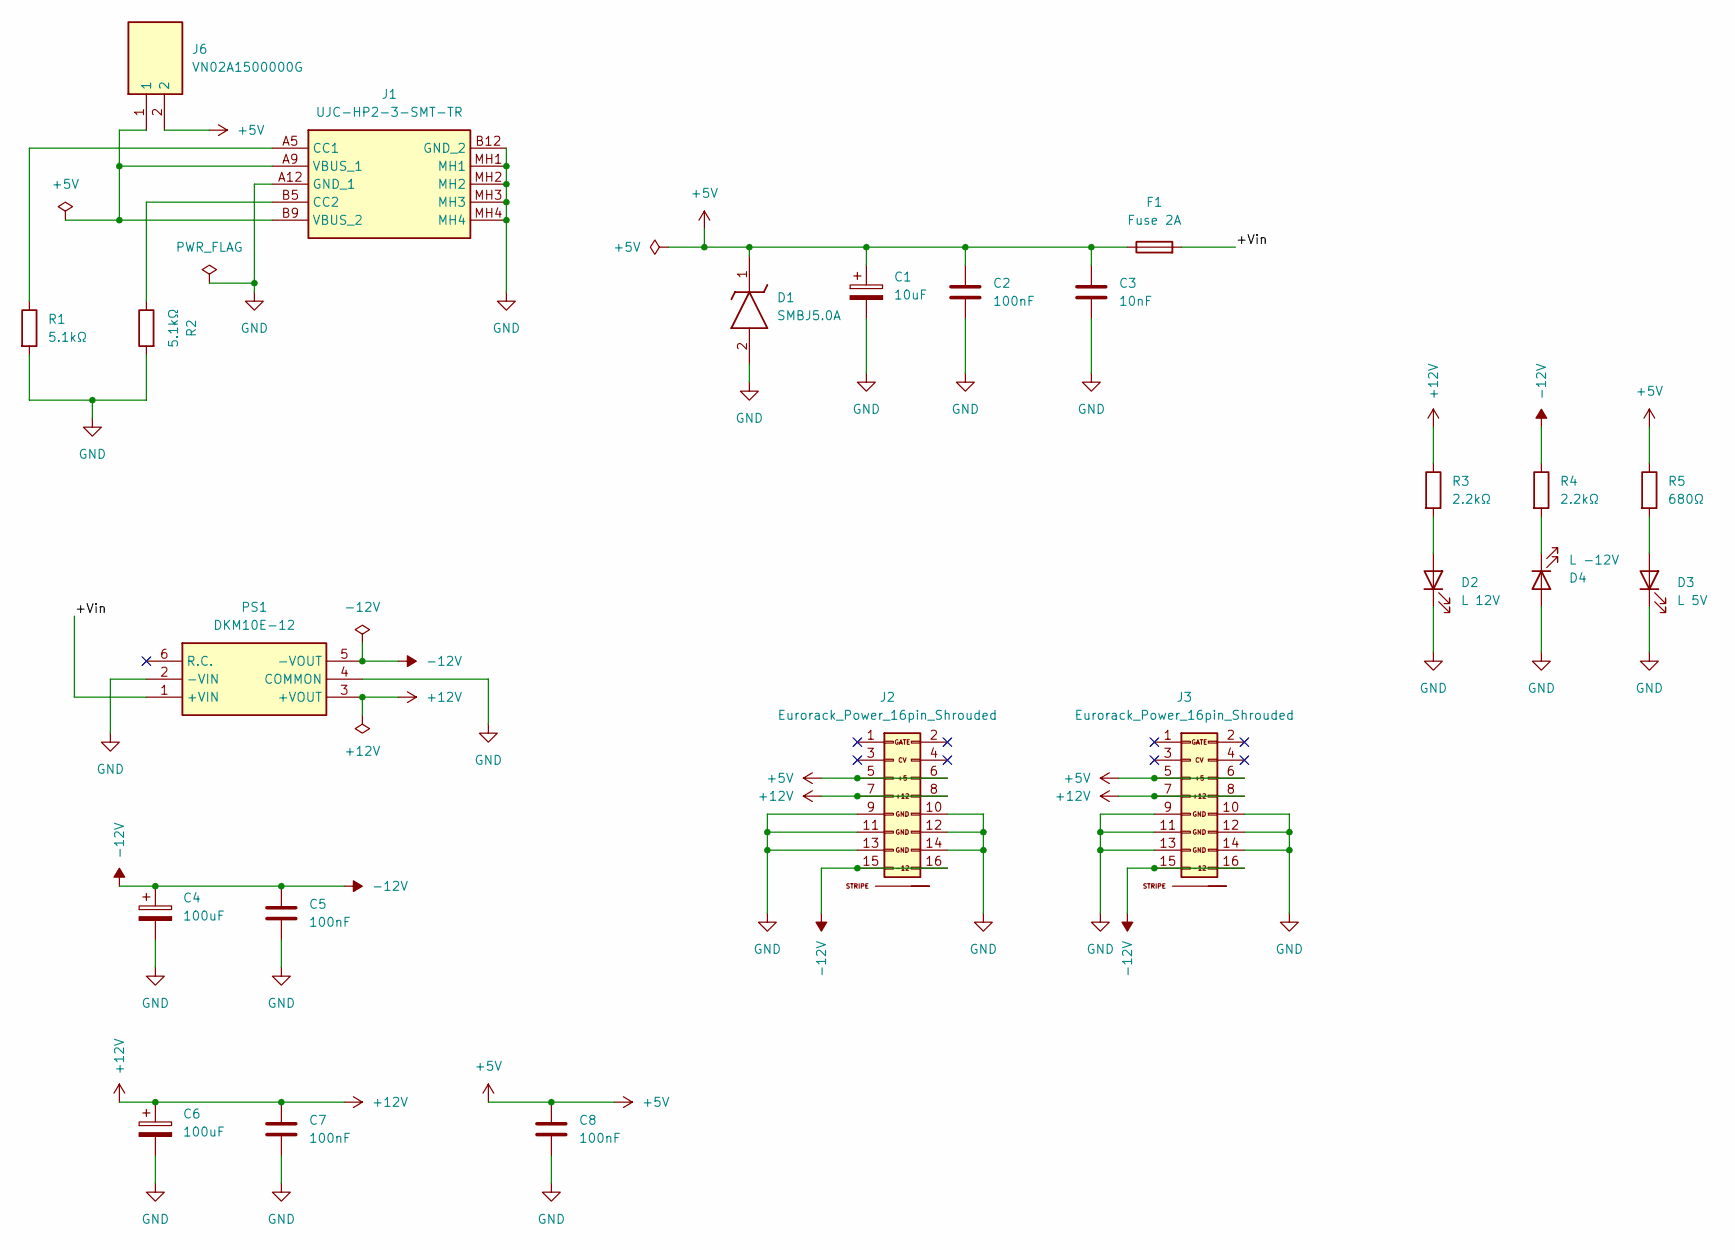
[picture p9: schematic V3.0.kicad_sch]

Parts:
C1: 10uF; CP_Elec_6.3x7.7; LCSC Part Number C72482
C2, C5, C7, C8: 100nF; C_0603_1608Metric; LCSC Part Number C14663
C3: 10nF; C_0603_1608Metric; LCSC Part Number C100042
C4, C6: 100uF; CP_Elec_6.3x7.7; LCSC Part Number C48587228
D1: SMBJ5.0A; DIOM5436X244N; Mouser Part Number 652-SMBJ5.0A
D2: L 12V; LED_D2.0mm_W4.8mm_H2.5mm_FlatTop; LCSC Part Number C6717903
D3: L 5V; LED_D2.0mm_W4.8mm_H2.5mm_FlatTop; LCSC Part Number C6717903
D4: L -12V; LED_D2.0mm_W4.8mm_H2.5mm_FlatTop; LCSC Part Number C6717903
F1: Fuse 2A; Fuse_1812_4532Metric; LCSC Part Number C135364
J1: UJC-HP2-3-SMT-TR; UJCHP23SMTTR; Mouser Part Number 179-UJC-HP2-3-SMT-TR
J2, J3: Eurorack_Power_16pin_Shrouded; Pins_2x08_2.54mm_TH_EuroPower_Shrouded_reducedsilk; Part Number LL1007-1 (2*8 HITEMP)
J6: VN02A1500000G; Mouser Part Number 649-VN02A15000J0G
PS1: DKM10E-12; DKM10E12; Mouser Part Number 709-DKM10E-12
R1, R2: 5.1kΩ; R_1206_3216Metric; LCSC Part Number C26033
R3, R4: 2.2kΩ; R_1206_3216Metric; LCSC Part Number C17948
R5: 680Ω; R_1206_3216Metric; LCSC Part Number C17975

Connections:
+5V: C1.1, C2.1, C3.1, C8.1, D1.1 (K), F1.1, J2.5 (+12V), J2.6, J3.5 (+12V), J3.6, J6.2, R5.1
+12V: C6.1, C7.1, J2.7 (12V), J2.8 (+12V), J3.7 (12V), J3.8 (+12V), PS1.3 (+VOUT), R3.1
+Vin: F1.2, PS1.1 (+VIN)
-12V: C4.1, C5.1, J2.15 (-12V), J2.16, J3.15 (-12V), J3.16, PS1.5 (-VOUT), R4.1
GND: C1.2, C2.2, C3.2, C4.2, C5.2, C6.2, C7.2, C8.2, D1.2 (A), D2.1 (K), D3.1 (K), D4.2 (A), J1.A12 (GND_1), J1.B12 (GND_2), J1.MH1, J1.MH2, J1.MH3, J1.MH4, J2.9 (GND), J2.10 (GND), J2.11 (GND), J2.12 (GND), J2.13 (-12), J2.14 (-12V), J3.9 (GND), J3.10 (GND), J3.11 (GND), J3.12 (GND), J3.13 (-12), J3.14 (-12V), PS1.2 (-VIN), PS1.4 (COMMON), R1.2, R2.2
unnamed: D2.2 (A), R3.2
unnamed: D3.2 (A), R5.2
unnamed: D4.1 (K), R4.2
unnamed: J1.A5 (CC1), R1.1
unnamed: J1.A9 (VBUS_1), J1.B9 (VBUS_2), J6.1
unnamed: J1.B5 (CC2), R2.1
